fpga-theremin/theremin/teensy4theremin/ltspice/diff_osc_dewster_2020-11-15_experiments_v7.asc

Cant: cap; 8pF
Chand: cap; 0.0001pF
L1: ind; 4mH; Rser=120 Cpar=1.2pF
Q1: npn; 2N3904
Q2: npn; 2N3904
Q3: npn; 2N3904
Q4: npn; 2N3904
Q5: npn; 2N3904
Q6: npn; 2N3904
Q7: npn; 2N3904
Q8: npn; 2N3904
Q9: npn; 2N3904
Q10: npn; 2N3904
Q11: pnp; 2N3906
Q12: pnp; 2N3906
Q13: npn; 2N3904
Q14: pnp; 2N3906
Q15: pnp; 2N3906
Q16: pnp; 2N3906
R1: res; 220
R2: res; 220
R3: res; 2200
R4: res; 1K
R5: res; 330
R6: res; 10
R7: res; 220
R8: res; 10
R10: res; 1
R11: res; 10
Rrf: res; 1Meg
V1: voltage; 3.3v
Named nets: 0, VCC, ANT
.tran 0 1.01m 1m 0.00001m
.IC V(ANT)=1
.MEAS TRAN t1 V(OUT) WHEN V(OUT) = 0 rise=1
.MEAS TRAN t2 V(OUT) WHEN V(OUT) = 0 rise=2
.MEAS TRAN freq21 PARAM 1/(t2-t1)
