fpga-theremin/theremin/teensy4theremin/ltspice/2020_npn_pnp_osc_test_v16.asc

C1: cap; 330pF
C2: cap; 100pF
C3: cap; 330pF
C4: cap; 1µF
C5: cap; 330pF
C6: cap; 330pF
C7: cap; 120pF
C8: cap; 4.7pF
C9: cap; 4.7pF
C10: cap; 0.5pF
C11: cap; 0.5pF
C12: cap; 0.5pF
C13: cap; 0.5pF
C14: cap; 2.2pF
C15: cap; 110pF
C16: cap; 330pF
C17: cap; 75pF
C18: cap; 330pF
Cant1: cap; 8pF
Cant: cap; 8pF
Chand1: cap; 1.5pF
Chand: cap; 1.5pF
D3: diode
D4: diode
D6: diode
D7: diode
L1: ind; 1.8mH; Ipk=0.1 Rser=82 Rpar=20Meg Cpar=1.286pF
L2: ind; 2.2mH; Ipk=0.1 Rser=82 Rpar=20Meg Cpar=1.286pF
Q1: npn; BC847B
Q2: pnp; BC857B
Q3: npn; BC847B
Q4: pnp; BC857B
Q5: npn; BC847B
Q6: npn; BC847B
Q7: pnp; BC857B
Q8: pnp; BC857B
R1: res; 120K
R2: res; 12400K
R3: res; 47
R4: res; 10
R5: res; 47
R6: res; 1200
R7: res; 120K
R8: res; 1200
R9: res; 1
R10: res; 1
R11: res; 47
R12: res; 47
R13: res; 220K
R14: res; 220K
R15: res; 1
R16: res; 2.2K
R17: res; 10
R18: res; 100
R19: res; 2400K
R20: res; 1
R21: res; 220K
R22: res; 1
R23: res; 2.2K
R24: res; 100
R25: res; 1
R26: res; 1.2Meg
V1: voltage; 3.3V
Named nets: 0, ANT, COM, ESD1, ESD2, FLT3V3, OSC_OUT, ANT2
.tran 0 2.5m 0.5m 0.00001m
.IC V(ANT)=1u
.MEAS TRAN t_var1 V(ANT) WHEN V(ANT) = 0 rise=1
.MEAS TRAN t_var2 V(ANT) WHEN V(ANT) = 0 rise=2
.MEAS TRAN f_var PARAM 1/(t_var2-t_var1)
ESD protection
Oscillator
Theremin oscillator - Colpitts with bridge
.ic V(ANT2)=1u
