fpga-theremin/theremin/teensy4theremin/ltspice/2019_analog_oscill_sin_33v_noise_test_v03.asc

C1: cap; 4.7pF
C2: cap; 120pF
C3: cap; 180pF
C4: cap; 10µF
C5: cap; 1pF
C6: cap; 33pF
C7: cap; 1pF
C8: cap; 1.5pF
C9: cap; 1.5pF
C10: cap; 1.5pF
C11: cap; 1.5pF
C12: cap; 1.5pF
C13: cap; 1.5pF
C14: cap; 4.7pF
C15: cap; 2.4nF
C16: cap; 240pF
C17: cap; 1µF
C18: cap; 1µF
Cant1: cap; 4pF
Chand: cap; 0.0001pF
D1: diode
D2: diode
D3: diode
D4: diode
D6: diode
D7: diode
L1: ind; 1.5mH; Ipk=0.1 Rser=120 Rpar=9Meg Cpar=1.76pF
L2: ind; 10µH; Rser=1
L4: ind; 100µH; Rser=10
Q1: npn; 2N3904
Q2: npn; 2N3904
Q3: npn; 2N3904
Q4: pnp; 2N3906
R1: res; 330k
R2: res; 1500
R3: res; 10
R4: res; 470K
R5: res; 180
R6: res; 1Meg
R7: res; 1500
R16: res; 3.6K
R17: res; 220
R18: res; 470
R19: res; 220
R20: res; 100
R21: res; 10
Rant: res; 2.4Meg
V1: voltage; 5V
V10: voltage; SINE(0 0.1 10000 0); Rser=100
V11: voltage; SINE(0 0.1 12725 0); Rser=100
V12: voltage; SINE(0 0.1 16192 0); Rser=100
V13: voltage; SINE(0 0.1 20604 0); Rser=100
V14: voltage; SINE(0 0.1 26218 0); Rser=100
V15: voltage; SINE(0 0.1 33362 0); Rser=100
V16: voltage; SINE(0 0.1 42453 0); Rser=100
V17: voltage; SINE(0 0.1 54020 0); Rser=100
V18: voltage; SINE(0 0.1 68740 0); Rser=100
V19: voltage; SINE(0 0.1 87470 0); Rser=100
V20: voltage; SINE(0 0.1 111303 0); Rser=100
V21: voltage; SINE(0 0.1 141631 0); Rser=100
V22: voltage; SINE(0 0.1 180223 0); Rser=100
V23: voltage; SINE(0 0.1 229330 0); Rser=100
V24: voltage; SINE(0 0.1 291818 0); Rser=100
V25: voltage; SINE(0 0.1 371332 0); Rser=100
V26: voltage; SINE(0 0.1 472512 0); Rser=100
V27: voltage; SINE(0 0.1 601262 0); Rser=100
V28: voltage; SINE(0 0.1 765094 0); Rser=100
V29: voltage; SINE(0 0.1 973566 0); Rser=100
V30: voltage; SINE(0 0.1 1238843 0); Rser=100
V31: voltage; SINE(0 0.1 1576403 0); Rser=100
V32: voltage; SINE(0 0.1 2005940 0); Rser=100
V33: voltage; SINE(0 0.1 2552518 0); Rser=100
V34: voltage; SINE(0 0.1 3248027 0); Rser=100
V35: voltage; SINE(0 0.1 4133048 0); Rser=100
V36: voltage; SINE(0 0.1 5259219 0); Rser=100
V37: voltage; SINE(0 0.1 6692248 0); Rser=100
V38: voltage; SINE(0 0.1 8515749 0); Rser=100
V39: voltage; SINE(0 0.1 10836117 0); Rser=100
V40: voltage; SINE(0 0.1 13788737 0); Rser=100
V41: voltage; SINE(0 0.1 17545886 0); Rser=100
V42: voltage; SINE(0 0.1 22326781 0); Rser=100
V43: voltage; SINE(0 0.1 28410373 0); Rser=100
V44: voltage; SINE(0 0.1 36151619 0); Rser=100
V45: voltage; SINE(0 0.1 46002197 0); Rser=100
V46: voltage; SINE(0 0.1 58536855 0); Rser=100
V47: voltage; SINE(0 0.1 74486952 0); Rser=100
V48: voltage; SINE(0 0.1 94783124 0); Rser=100
V49: voltage; SINE(0 0.1 120609589 0); Rser=100
Named nets: 0, ANT, OSC_OUT, COM, ESD1, OUT, ESD2, OUT_FLT, TEST_SINES
.tran 0 21m 1m
.IC V(ANT)=1u
.MEAS TRAN t_var1 V(ANT) WHEN V(ANT) = 0 rise=1
.MEAS TRAN t_var2 V(ANT) WHEN V(ANT) = 0 rise=2
.MEAS TRAN f_var PARAM 1/(t_var2-t_var1)
ESD protection SP721
