fpga-theremin/theremin/teensy4theremin/ltspice/2020_filter_experiments_v2.asc

C1: cap; 1.6nF
C2: cap; 820pF
C3: cap; 1.6nF
C4: cap; 820pF
C5: cap; 1.6nF
L1: ind; 22µH; Rser=1
L2: ind; 47µH; Rser=2
L3: ind; 22µH; Rser=1
L4: ind; 47µH; Rser=2
L5: ind; 22µH; Rser=1
R1: res; 100
R2: res; 1000
V1: voltage; SINE(0 1 {FTEST}); Rser=1
Named nets: 0, OUT
.tran 0 9m 1m 0.0000001m
.STEP PARAM FTEST LIST 50000 58229 67813 78975 91973 107111 124740 145271 169180 197026 229454 267219 311200 362420 422071 491539 572440 666657 776381 904165 1052980 1226289 1428122 1663174 1936913 2255707 2626971 3059340 3562872 4149280 4832204 5627529 6553756 7632429 8888639 10351607 12055363 14039537 16350284 19041353
