fpga-theremin/theremin/teensy4theremin/ltspice/2020_oscillator_experiments_v12.asc

C1: cap; 150pF
C2: cap; 1µF
C7: cap; 0.5pF
C10: cap; 0.5pF
C11: cap; 0.5pF
C12: cap; 0.5pF
C13: cap; 512pF
C14: cap; 0.5pF
C16: cap; 0.5pF
C17: cap; 0.5pF
C18: cap; 0.5pF
C21: cap; 224pF
C23: cap; 0.1µF
C_ant: cap; 8pF
C_hand: cap; 0.01pF
C_sense: cap; 1pF
D1: diode
D2: diode
D3: diode
D4: diode
D5: diode
D6: diode
D7: diode
D8: diode
L1: ind; 3mH; Rser=120 Rpar=20Meg
L4: ind; 128µH; Rser=10
L5: ind; 61µH; Rser=5
R4: res; 1000
R5: res; 1000
R7: res; 1
R10: res; 3300
R16: res; 100
R19: res; 100
R20: res; 1000
R_loss: res; 2400K
R_sense: res; 3.6
U1: OPA350
U2: ad8611
V1: voltage; 3.3V
Named nets: 0, COM, ESD1, ESD2, ANT, L_IN2, L_OUT, ESD3, ESD4, FLT_OUT
.tran 0 1.3m 1m 0.000001m
.IC V(ANT)=1u
