fpga-theremin/theremin/teensy4theremin/ltspice/2020_npn_pnp_osc_v16_tune_4.asc

C1: cap; 82pF
C2: cap; 10pF
C3: cap; 150pF
C4: cap; 1µF
C5: cap; 82pF
C6: cap; 150pF
C8: cap; 10pF
C9: cap; 10pF
C10: cap; 0.5pF
C11: cap; 0.5pF
C12: cap; 0.5pF
C13: cap; 0.5pF
C14: cap; 150pF
Cant: cap; 8pF
Chand: cap; 100pF
D3: diode
D4: diode
D6: diode
D7: diode
L1: ind; 1.5mH; Ipk=0.1 Rser=40 Rpar=20Meg Cpar=1.286pF
Q1: npn; BC847B
Q2: pnp; BC857B
R1: res; 470K
R2: res; 2700K
R3: res; 47
R4: res; 10
R5: res; 47
R6: res; 15K
R7: res; 470K
R8: res; 15K
V1: voltage; 3.3V
Named nets: 0, ANT, COM, ESD1, ESD2, FLT3V3, OSC_OUT
.tran 0 8.1m 0.6m 0.00001m
.IC V(ANT)=1u
.MEAS TRAN t_var1 V(ANT) WHEN V(ANT) = 0 rise=1
.MEAS TRAN t_var2 V(ANT) WHEN V(ANT) = 0 rise=2
.MEAS TRAN f_var PARAM 1/(t_var2-t_var1)
ESD protection
Oscillator
Theremin oscillator - Colpitts with bridge
