fpga-theremin/theremin/teensy4theremin/ltspice/2020_npn_pnp_osc_v16_tune.asc

C1: cap; 330pF
C3: cap; 330pF
C4: cap; 1µF
C5: cap; 330pF
C6: cap; 330pF
C8: cap; 4.7pF
C9: cap; 4.7pF
C10: cap; 0.5pF
C11: cap; 0.5pF
C12: cap; 0.5pF
C13: cap; 0.5pF
Cant: cap; 8pF
Chand: cap; 0.1pF
D3: diode
D4: diode
D6: diode
D7: diode
L1: ind; 1.8mH; Ipk=0.1 Rser=82 Rpar=20Meg Cpar=1.286pF
Q1: npn; BC847B
Q2: pnp; BC857B
R1: res; 120K
R2: res; 2700K
R3: res; 47
R4: res; 10
R5: res; 47
R6: res; 1000
R7: res; 120K
R8: res; 1000
V1: voltage; 3.3V
Named nets: 0, ANT, COM, ESD1, ESD2, FLT3V3, OSC_OUT
.tran 0 1.1m 0.1m 0.00001m
.IC V(ANT)=1u
.MEAS TRAN t_var1 V(ANT) WHEN V(ANT) = 0 rise=1
.MEAS TRAN t_var2 V(ANT) WHEN V(ANT) = 0 rise=2
.MEAS TRAN f_var PARAM 1/(t_var2-t_var1)
ESD protection
Oscillator
Theremin oscillator - Colpitts with bridge
