fpga-theremin/theremin/teensy4theremin/ltspice/2020_analog_oscill_npn_experiments_33v_v05.asc

C1: cap; 1pF
C2: cap; 2.2pF
C3: cap; 2.2pF
C4: cap; 1µF
C5: cap; 1pF
C6: cap; 220pF
C7: cap; 220pF
C8: cap; 0.5pF
C9: cap; 0.5pF
C10: cap; 0.5pF
C11: cap; 0.5pF
C12: cap; 0.5pF
C13: cap; 0.5pF
C15: cap; 22pF
Cant: cap; 8pF
Chand: cap; {CHAND}
D1: diode
D2: diode
D3: diode
D4: diode
D6: diode
D7: diode
L1: ind; 2.2mH; Ipk=0.1 Rser=69 Rpar=1.536Meg Cpar=1.147pF
Q1: npn; 2N3904
Q2: npn; 2N3904
R1: res; 470
R2: res; 100K
R3: res; 100K
R4: res; 10
R5: res; 470
R7: res; 33K
Rant: res; 4.7Meg
V1: voltage; 3.3V
Named nets: 0, ANT, COM, ESD1, ESD2, ESD3, OUT_SIN2, OUT
.tran 0 4m 3m 0.001m
.STEP PARAM CHAND LIST 0pF 1.5pF
.IC V(ANT)=1u
.MEAS TRAN t_var1 V(ANT) WHEN V(ANT) = 0 rise=1
.MEAS TRAN t_var2 V(ANT) WHEN V(ANT) = 0 rise=2
.MEAS TRAN f_var PARAM 1/(t_var2-t_var1)
ESD protection SP721
