fpga-theremin/theremin/teensy4theremin/ltspice/phase_shift_sensor_2500uH_serial_lc_v5_0125mm_experiments.asc

C1: cap; 3.3pF
C2: cap; 220pF
C3: cap; 3.3pF
C4: cap; 3.3pF
C6: cap; 0.5pF
C7: cap; 0.5pF
C8: cap; 0.5pF
C9: cap; 0.5pF
Cant: cap; 8pF
Chand: cap; {Chand}
D3: diode
D4: diode
D5: diode
D6: diode
L1: ind; 2500µH; Ipk=0.01 Rser=79 Rpar=2.828Meg Cpar=1.166pF
R1: res; 10
R2: res; 220K
R3: res; 220K
R4: res; 4.7Meg
U1: 74AHC1G04
U2: 74AHC1G04
U3: 74AHC1G04
U4: 74AHC1G14
U5: 74AHC1G04
U6: 74AHC1G04
V1: voltage; 3.3V
V2: voltage; PULSE(0 3.3 0 0.00000001 0.00000001 0.000000500 0.000001000)
V3: voltage; 3.3V
Named nets: 0, FREF, ANT, COM, FSHIFT, OUT_SHIFTED, FREF_BUF, 5V
.tran 0 0.000305 0.0003 0.000000001
.step param Chand list 0pF 0.025pF 0.05pF 0.075pF 0.1pF 0.125pF 0.15pF 0.175pF 0.2pF 0.225pF 0.25pF 0.275pF 0.3pF 0.325pF 0.35pF 0.375pF 0.4pF 0.425pF 0.45pF 0.475pF 0.5pF 0.525pF 0.55pF 0.575pF 0.6pF 0.625pF 0.65pF 0.675pF 0.7pF 0.725pF 0.75pF 0.775pF 0.8pF 0.825pF 0.85pF 0.875pF 0.9pF 0.925pF 0.95pF 0.975pF 1pF 1.025pF 1.05pF 1.075pF 1.1pF 1.125pF 1.15pF 1.175pF 1.2pF 1.225pF 1.25pF 1.275pF 1.3pF 1.325pF 1.35pF 1.375pF 1.4pF 1.425pF 1.45pF 1.475pF 1.5pF 1.525pF 1.55pF 1.575pF 1.6pF 1.625pF 1.65pF 1.675pF 1.7pF 1.725pF 1.75pF 1.775pF 1.8pF 1.825pF 1.85pF 1.875pF 1.9pF 1.925pF 1.95pF 1.975pF 2.0pF
Ref clock ~0.5..1.5 MHz 3.3V
Phase Shift Theremin Sensor
Air core 32mm plastic frame 0.125 mm copper wire 
coil-to-coil, 53mm winding length
ESD protection SP721
Calibration: with hand FAR from antenna,
choose FREF so phase shift of output changes maximally 
when C_hand changes by smal value
Simulate for hand C from 0 to 2pF with 0.025pF step
