fpga-theremin/theremin/hardware/oscillator/2018_09_colpitts_npn_oscillator_v3.asc

C1: cap; 4.7pF
C2: cap; 220pF
C3: cap; 220pF
C4: cap; 1µF
C5: cap; 0.1µF
C6: cap; 3.5pF
C7: cap; 3.5pF
C8: cap; 0.01µF
C10: cap; 1pF
C12: cap; 3.5pF
C13: cap; 3.5pF
Cant: cap; 7pF
D1: diode
D2: diode
D7: diode
D8: diode
L1: ind; 1.45mH; Ipk=0.1 Rser=65 Rpar=20Meg Cpar=0.85pF
R1: res; 470k
R2: res; 2.7k
R3: res; 100
R4: res; 1Meg
R5: res; 1Meg
Rant: res; 10meg
U1: npn; BC547C
U2.1: 74hc04; VCC=3.3  SPEED=1.0  TRIPDT=1e-9
U2.2: 74hc04; VCC=3.3  SPEED=1.0  TRIPDT=1e-9
V1: voltage; 3.3v
Named nets: 0, 3.3V, ANT, OUT_OSC, OUT, ESD1, ESD2
.tran 0 15m 1m
.IC V(ANT)=1u
.MEAS TRAN t_var1 V(ANT) WHEN V(ANT) = 0 rise=1
.MEAS TRAN t_var2 V(ANT) WHEN V(ANT) = 0 rise=2
.MEAS TRAN f_var PARAM 1/(t_var2-t_var1)
Digital Theremin Sensor Oscillator v0.1
ESD protection diode array, e.g. DALC208SC6
Oscillator
Output buffer
