fpga-theremin/theremin/teensy4theremin/ltspice/2020_current_sense_lt1713.asc

C2: cap; 10µF
C_ant: cap; 10pF
L1: ind; 4.624mH; Rser=120 Rpar=10Meg Cpar=1.216pF
R1: res; 1
R2: res; 10000
R3: res; 1
R4: res; 1
R5: res; 1
R_loss: res; 7000K
R_sense: res; 47
U1: LT1713
U2: max961b
V1: voltage; 3.3V
Named nets: 0, COM, ANT
.tran 0 1m 0.01m
.IC V(ANT)=1u
