fpga-theremin/theremin/teensy4theremin/ltspice/2020_current_sense_lt1809_v01.asc

C2: cap; 10µF
C_ant: cap; 8pF
L1: ind; 4.624mH; Rser=120 Rpar=100Meg Cpar=1.216pF
R1: res; 1
R2: res; 330
R3: res; 100
R4: res; 100
R_loss: res; 7000K
R_sense: res; 22
U1: LT6200-10
V1: voltage; 4.5V
Named nets: 0, COM, ANT
.tran 0 3m 1m 0.00001m
.IC V(ANT)=1u
