fpga-theremin/theremin/teensy4theremin/ltspice/2020_current_sense_lt6200_v02.asc

C2: cap; 10µF
C_ant: cap; 10pF
L1: ind; 4.624mH; Rser=120 Rpar=100Meg Cpar=1.216pF
R1: res; 1
R2: res; 2k
R3: res; 470
R4: res; 470
R5: res; 1
R_loss: res; 7000K
R_sense: res; 100
U1: opa354
V1: voltage; 4.5V
Named nets: 0, COM, ANT
.tran 0 3m 1m 0.00001m
.IC V(ANT)=1u
