fpga-theremin/theremin/teensy4theremin/ltspice/2020_current_sense_npn_pnp_v03.asc

C1: cap; 10000pF
C2: cap; 1pF
C3: cap; 1pF
C_ant: cap; 10pF
D1: diode
D2: diode
L1: ind; 4.624mH; Rser=120 Rpar=100Meg Cpar=1.216pF
Q1: pnp; BC557C
Q2: npn; BC547C
Q3: npn; BC547C
Q8: pnp; BC557C
Q10: pnp; BC557C
Q11: pnp; BC557C
Q12: pnp; BC557C
Q13: pnp; BC557C
Q14: npn; BC547C
Q15: npn; BC547C
Q16: npn; BC547C
Q17: npn; BC547C
Q18: npn; BC547C
R1: res; 100
R3: res; 22
R4: res; 22
R6: res; 100K
R7: res; 1K
R8: res; 1K
R9: res; 100K
R10: res; 10
R11: res; 1K
R12: res; 10
R13: res; 4.7K
R_loss: res; 7500K
R_sense: res; 33
U1: 74AHC1G04
V1: voltage; 4.5V
V2: voltage; 3.3V
Named nets: 0, COM, ANT, OUT
.tran 0 0.503m 0.5m 0.00001m
.IC V(ANT)=1u
