fpga-theremin/theremin/teensy4theremin/ltspice/2020_pll_4046_v01.asc

C1: cap; 10nF
C2: cap; 3300pF
C3: cap; 0.1µF
C_ant1: cap; 10pF
L1: ind; 4.624mH; Rser=120 Rpar=10Meg Cpar=1.216pF
R1: res; 22K
R3: res; 27K
R4: res; 1K
R6: res; 4.3K
R7: res; 100K
R13: res; 1K
R_loss1: res; 7000K
R_sense: res; 33
U1: opa354
U2: 74HC4046TI
U3: opa354
U4: opa354
V1: voltage; 5V
Named nets: COM, 0, ANT, VCOCTL
.tran 0 3m 0.001m
