fpga-theremin/theremin/teensy4theremin/ltspice/2020_current_sense_comparator_npn_v09.asc

C2: cap; 22µF
C_ant: cap; 9.8pF
L1: ind; 2.624mH; Rser=66 Cpar=1.216pF
Q1: npn; BC547C
Q2: npn; BC547C
Q3: npn; BC547C
Q4: npn; BC547C
Q5: npn; BC547C
Q6: npn; BC547C
Q7: npn; BC547C
Q8: npn; BC547C
Q9: npn; BC547C
R1: res; 1
R3: res; 270
R4: res; 100
R16: res; 4.,7K
R19: res; 4.7K
R_loss: res; 7.6Meg
R_sense: res; 47
V1: voltage; 4.5V
Named nets: 0, COM, ANT, Drive, diff1, OUT
.tran 0 3m 1m 0.00001m
.IC V(ANT)=1u
