fpga-theremin/theremin/teensy4theremin/ltspice/2020_current_sense_ad6362_v02.asc

C1: cap; 150pF
C2: cap; 0.1µF
C3: cap; 0.1µF
C4: cap; 10pF
C5: cap; 0.1µF
C_ant: cap; 8pF
L1: ind; 2.624mH; Rser=60 Rpar=10Meg Cpar=1.216pF
Q1: pnp; BC557C
Q2: npn; BC547C
R1: res; 1
R2: res; 10K
R3: res; 10K
R4: res; 4.7K
R5: res; 4.7K
R6: res; 1
R7: res; 22K
R8: res; 22K
R9: res; 100
R10: res; 100
R11: res; 100
R_loss: res; 1000K
R_sense: res; 100
U1: LTC6362
U2: LTC6362
V1: voltage; 4.5V
Named nets: 0, COM, ANT
.tran 0 3m 1m 0.00001m
.IC V(ANT)=1u
