fpga-theremin/theremin/teensy4theremin/ltspice/2020_current_sense_comparator_ltc6362_v04.asc

C1: cap; 3pF
C2: cap; 0.1µF
C3: cap; 3pF
C4: cap; 220pF
C5: cap; 1nF
C6: cap; 100pF
C7: cap; 100pF
C8: cap; 100pF
C9: cap; 1nF
C10: cap; 10pF
C11: cap; 10pF
C12: cap; 1000pF
C_ant: cap; 8pF
L1: ind; 2.624mH; Rser=66 Rpar=10Meg Cpar=1.216pF
R1: res; 1
R2: res; 10K
R3: res; 10K
R4: res; 1000
R6: res; 22K
R7: res; 22K
R8: res; 100
R9: res; 100
R10: res; 100
R11: res; 470K
R12: res; 1000
R13: res; 1000
R14: res; 33k
R15: res; 33k
R17: res; 1
R_loss: res; 1Meg
R_sense: res; 100
U1: LTC6362
U2: LTC6362
V1: voltage; 3.3V
Named nets: 0, COM, ANT
.tran 0 1.5m 0.5m 0.00001m
.IC V(ANT)=1u
