fpga-theremin/theremin/teensy4theremin/ltspice/2020_current_sense_comparator_npn_pnp_v03.asc

C1: cap; 10nF
C2: cap; 0.1µF
C3: cap; 10nF
C4: cap; 10nF
C5: cap; 1nF
C6: cap; 100pF
C7: cap; 100pF
C8: cap; 100pF
C_ant: cap; 8pF
L1: ind; 2.624mH; Rser=66 Rpar=10Meg Cpar=1.216pF
Q1: npn; BC847C
Q2: npn; BC847C
Q3: npn; BC847C
Q4: npn; BC847C
Q5: pnp; BC857C
Q6: pnp; BC857C
Q7: pnp; BC857C
Q8: pnp; BC857C
Q9: npn; BC847C
Q10: pnp; BC857C
R1: res; 1
R2: res; 10K
R3: res; 10K
R4: res; 100
R5: res; 100
R6: res; 68K
R7: res; 68K
R8: res; 100
R9: res; 100
R10: res; 100
R11: res; 470K
R16: res; 4.7K
R18: res; 4.7K
R19: res; 4.7K
R_loss: res; 1Meg
R_sense: res; 100
U2: LTC6362
V1: voltage; 3.3V
Named nets: 0, COM, ANT, OUT, diff1, diff2
.tran 0 1.5m 1m 0.000001m
.IC V(ANT)=1u
