fpga-theremin/theremin/teensy4theremin/ltspice/2020_current_sense_comparator_sine_drive_osc_v01.asc

C1: cap; 1µF
C2: cap; 1µF
C7: cap; 0.5pF
C10: cap; 0.5pF
C_ant: cap; 8pF
C_hand: cap; 0.0001pF
D1: diode
D2: diode
L1: ind; 2.4mH; Rser=85 Rpar=10Meg Cpar=1.216pF
Q1: npn; 2N3904
Q2: pnp; 2N3906
Q3: npn; 2N3904
Q4: pnp; 2N3906
R1: res; 1
R2: res; 10K
R3: res; 10K
R4: res; 2.2K
R5: res; 1
R6: res; 2.2K
R7: res; 2.2K
R8: res; 2.2K
R9: res; 100
R10: res; 100
R11: res; 100
R47: res; 22
R_loss: res; 12400K
U2: ad8137
U7: LT1711
V1: voltage; 3.3V
V2: voltage; 3.3V
Named nets: 0, COM, ESD1, ANT, OUTN, OUTP
.tran 0 3.5m 1.5m 0.0001m
.IC V(ANT)=1u
