fpga-theremin/theremin/teensy4theremin/ltspice/2020_current_sense_comparator_square_drive_osc_v06_lt1711.asc

C1: cap; 10µF
C7: cap; 0.5pF
C10: cap; 0.5pF
C_ant: cap; 8pF
C_hand: cap; 0.0001pF
D1: diode
D2: diode
L1: ind; 2.4mH; Rser=85 Rpar=10Meg Cpar=1.216pF
R1: res; 1
R2: res; 100
R3: res; 100
R4: res; 100
R5: res; 100
R6: res; 100
R7: res; 100
R8: res; 1000
R9: res; 10
R47: res; 100
R_loss: res; 1000K
U7: LT1711
V1: voltage; 3.3V
Named nets: 0, COM, ESD1, ANT, POUT, NOUT
.tran 0 1.3m 0.3m 0.00001m
.IC V(ANT)=1u
