fpga-theremin/theremin/teensy4theremin/ltspice/2020_current_sense_comparator_square_drive_osc_v07.asc

C1: cap; 10µF
C2: cap; 820pF
C3: cap; 3.3nF
C4: cap; 820pF
C5: cap; 0.1µF
C6: cap; 0.1µF
C7: cap; 1pF
C10: cap; 1pF
C_ant: cap; 10pF
C_hand: cap; 0.0001pF
D1: diode
D2: diode
L1: ind; 2.4mH; Rser=85 Rpar=10Meg Cpar=1.216pF
L2: ind; 33µH; Rser=5
L3: ind; 8.2µH; Rser=3
L4: ind; 33µH; Rser=5
R1: res; 1
R2: res; 100
R3: res; 100
R4: res; 100
R5: res; 100
R6: res; 1000
R47: res; 22
R_loss: res; 2400K
U1: LTC6752
U2: LTC6754
V1: voltage; 3.3V
Named nets: 0, COM, ESD1, ANT, OUT, OUTP, OUTN
.tran 0 5.2m 0.2m 0.00001m
.IC V(ANT)=1
