fpga-theremin/theremin/teensy4theremin/ltspice/2020_current_sense_comparator_square_drive_osc_v09_simple.asc

C1: cap; 8pF
L1: ind; 2.624mH; Rser=66 Rpar=10Meg Cpar=1.216pF
R2: res; 100
R3: res; 470
R_loss: res; 2Meg
R_sense: res; 47
U7: LT1711
V1: voltage; 3.3V
Named nets: 0, COM, OUT, ANT
.tran 0 1.3m 0.3m 0.000001m
.IC V(ANT)=1u
