fpga-theremin/theremin/teensy4theremin/ltspice/2020_current_sense_comparator_square_drive_sine_out_osc_v02.asc

C1: cap; 1µF
C2: cap; 0.1µF
C3: cap; 100pF
C4: cap; 100pF
C5: cap; 150pF
C7: cap; 0.5pF
C10: cap; 0.5pF
C_ant: cap; 8pF
C_hand: cap; 0.001pF
D1: diode
D2: diode
L1: ind; 2.4mH; Rser=85 Rpar=10Meg Cpar=1.216pF
R1: res; 1
R2: res; 47
R3: res; 47K
R4: res; 47K
R5: res; 15K
R6: res; 15K
R7: res; 47
R8: res; 1000
R9: res; 100
R10: res; 220
R11: res; 470K
R47: res; 100
R_loss: res; 2200K
U1: LT1711
U3: LTC6362
V1: voltage; 3.3V
Named nets: 0, COM, ESD1, ANT, outp, outn
.tran 0 1.2m 0.2m 0.00001m
.IC V(ANT)=1
