fpga-theremin/theremin/teensy4theremin/ltspice/diff_osc_2020-11-15.asc

C1: cap; 0.01µf
Cant: cap; 10pF
L1: ind; 4mH
Q1: npn; 2N3904
Q2: npn; 2N3904
Q3: npn; 2N3904
Q4: npn; 2N3904
Q5: npn; 2N3904
Q6: npn; 2N3904
R1: res; 47
R2: res; 4.7k
R3: res; 4.7k
R4: res; 100
R5: res; 4.7k
R6: res; 100
Rrf: res; 1Meg
V1: voltage; 3.3v
Named nets: 0, VCC, OUT
.TRAN 0 1m 0.997m
.IC V(OUT)=0
.MEAS TRAN t1 V(OUT) WHEN V(OUT) = 0 rise=1
.MEAS TRAN t2 V(OUT) WHEN V(OUT) = 0 rise=2
.MEAS TRAN freq21 PARAM 1/(t2-t1)
