fpga-theremin/theremin/teensy4theremin/ltspice/2020_current_sense_bjt_v04.asc

C1: cap; 8pF
C2: cap; 0.1µF
C3: cap; 220pF
C4: cap; 220pF
L1: ind; 2mH; Rser=85 Rpar=10Meg Cpar=1.216pF
Q1: npn; 2N3904
Q2: npn; 2N3904
Q3: npn; 2N3904
Q4: npn; 2N3904
Q5: pnp; 2N3906
Q6: pnp; 2N3906
Q7: pnp; 2N3906
Q8: npn; 2N3904
R1: res; 100
R2: res; 10K
R3: res; 10K
R6: res; 22
R7: res; 1K
R8: res; 470
R_loss: res; 2.4Meg
U1: LT1711
V1: voltage; 3.3V
Named nets: 0, COM, OUT
.tran 0 2.3m 0.3m 0.000001m
