fpga-theremin/theremin/teensy4theremin/ltspice/2020_current_sense_sin_v01.asc

C1: cap; 8pF
C2: cap; 820pF
C3: cap; 2.4nF
C4: cap; 8pF
L1: ind; 2mH; Rser=85 Rpar=10Meg Cpar=1.216pF
L2: ind; 24µH
L3: ind; 8.2µH
L4: ind; 2mH; Rser=85 Rpar=10Meg Cpar=1.216pF
R1: res; 100
R2: res; 100
R6: res; 12
R_loss1: res; 2.4Meg
R_loss: res; 2.4Meg
U1: LT1711
V1: voltage; 3.3V
Named nets: 0, COM, OUTP, OUTN
.tran 0 2.3m 0.3m 0.000001m
