fpga-theremin/theremin/teensy4theremin/ltspice/2020_current_sense_comparator_sin_drive_analod_diff_out_osc_v01.asc

C1: cap; 10µF
C2: cap; 390pF
C3: cap; 5.6nF
C5: cap; 0.1µF
C6: cap; 390pF
C7: cap; 0.5pF
C10: cap; 0.5pF
C_ant: cap; 8pF
C_hand: cap; 0.0001pF
D1: diode
D2: diode
L1: ind; 2.4mH; Rser=85 Rpar=10Meg Cpar=1.216pF
L2: ind; 56µH; Rser=8
L3: ind; 3.9µH; Rser=2.5
L5: ind; 56µH; Rser=8
R1: res; 1
R2: res; 1
R3: res; 1
R7: res; 1.3K
R8: res; 100
R10: res; 100
R11: res; 100
R13: res; 100
R_loss: res; 2400K
R_sense: res; 12
U1: AD1580
U7: LT1711
V1: voltage; 3.3V
Named nets: 0, COM, ESD1, ANT, OUTP, VREF, DRIVE, OUTN, AOUTP, AOUTN
.tran 0 1.3m 0.3m 0.00001m
.IC V(ANT)=1u
Bandpass filter: F_osc/1.3,,F_osc*1.3
Reference voltage 1.25V
Differential Sine output 
-500..+500mV
Current Sensing Theremin Oscillator on LT1711
