fpga-theremin/theremin/teensy4theremin/ltspice/2020_analog_theremin_v02.asc

C1: cap; 10µF
C2: cap; 2.4nF
C3: cap; 16nF
C4: cap; 0.1µF
C5: cap; 3.3nF
C6: cap; 6.8nF
C7: cap; 0.5pF
C8: cap; 47nF
C9: cap; 6.8nF
C10: cap; 0.5pF
C11: cap; 3nF
C12: cap; 2.2nF
C13: cap; 1nF
C_ant: cap; 8pF
C_hand: cap; 0.0001pF
C_tune: cap; 3.5pF
D1: diode
D2: diode
L1: ind; 2.266mH; Rser=80 Rpar=20Meg
L2: ind; 160µH; Rser=3
L3: ind; 24µH; Rser=0.5
L4: ind; 120µH; Rser=3
L5: ind; 240µH; Rser=3
L6: ind; 33µH; Rser=0.5
L7: ind; 240µH; Rser=3
Q1: npn; 2N3904
Q2: pnp; 2N3906
R1: res; 1
R2: res; 100
R3: res; 100
R4: res; 100
R5: res; 200
R6: res; 200
R7: res; 100
R8: res; 200
R9: res; 200
R10: res; 100
R11: res; 2000
R12: res; 2000
R13: res; 470
R14: res; 3.3K
R15: res; 1K
R16: res; 1.3K
R47: res; 12
R_loss: res; 2400K
U1: 74hc393
U2: 74hc393
U3: pot; R=25k; T=.99
U4: pot; R=25k; T=.1
U5: LMC555
U6: pot
U7: LT1711
V1: voltage; 5V
V_CRYSTAL_2MHz: voltage; PULSE(0 5 0 1ns 1ns 0.222u 0.5u)
Named nets: 0, COM, ESD1, ANT, OUT, OSC2, OSC4, OSC8, OSC16, REF2, REF4, REF8, REF16, EVEN, ODD
.tran 0 4.3m 0.3m
.IC V(ANT)=1u
