fpga-theremin/theremin/teensy4theremin/kicad/sensor/analog_switch_heterodyne/analog_switch_heterodyne.kicad_pcb

## KiCad design teensy4theremin/kicad/sensor/analog_switch_heterodyne/analog_switch_heterodyne.kicad_pcb (2020-02-23)

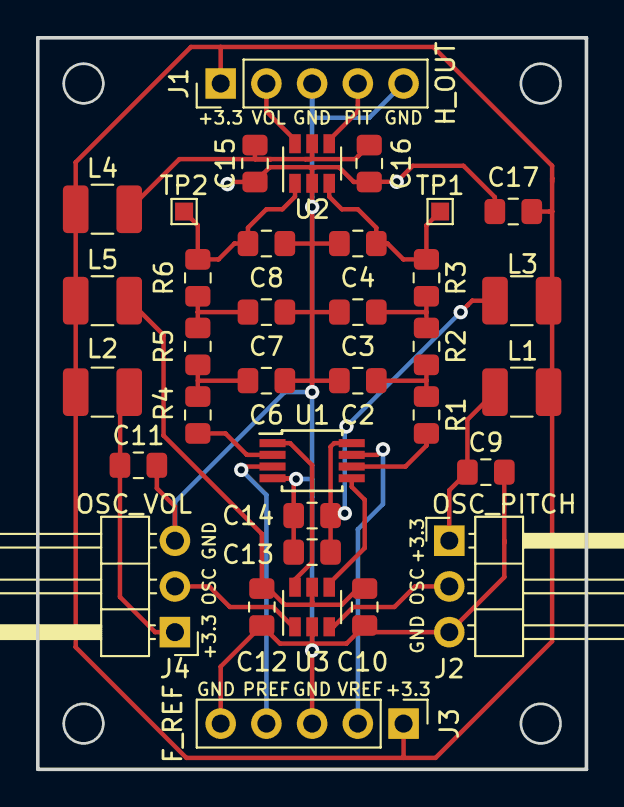
[picture p23: board analog_switch_heterodyne.kicad_pcb from above]

Board: 2 copper layers, 30.5 x 40.6 mm, 35 parts (0 on the bottom side), 23 nets.

Parts:
C2, C3, C4, C6, C7, C8: 100pF; C_0805_2012Metric_Pad1.15x1.40mm_HandSolder
C9, C11, C12, C13, C15: 1uF; C_0805_2012Metric_Pad1.15x1.40mm_HandSolder
C10, C14, C16: 0.1uF; C_0805_2012Metric_Pad1.15x1.40mm_HandSolder
C17: 2.2uF; C_0805_2012Metric_Pad1.15x1.40mm_HandSolder
J1: H_OUT; PinHeader_1x05_P2.54mm_Vertical
J2: OSC_PITCH; PinHeader_1x03_P2.54mm_Horizontal
J3: F_REF; PinHeader_1x05_P2.54mm_Vertical
J4: OSC_VOL; PinHeader_1x03_P2.54mm_Horizontal
L1, L2, L3, L4, L5: Ferrite 10uH; L_1210_3225Metric_Pad1.42x2.65mm_HandSolder
R1, R4: 100; R_0805_2012Metric_Pad1.15x1.40mm_HandSolder
R2, R5: 4.7K; R_0805_2012Metric_Pad1.15x1.40mm_HandSolder
R3, R6: 47K; R_0805_2012Metric_Pad1.15x1.40mm_HandSolder
TP1: PITCH_FLT; TestPoint_Pad_1.0x1.0mm
TP2: VOL_FLT; TestPoint_Pad_1.0x1.0mm
U1: ADG721BRMZ; MSOP-8_3x3mm_P0.65mm
U2, U3: 2G04; SOT-23-6

Connections:
+3V3: C17.1, J1.1, J3.1, L1.1, L2.1, L3.1, L4.1, L5.1
/3.3V_1: C9.1, J2.1, L1.2
/3.3V_2: C11.1, J4.1, L2.2
/FREF_PITCH: J3.4, U1.3
/FREF_VOL: J3.2, U1.7
/HOUT_PITCH: J1.4, U2.4
/HOUT_VOL: J1.2, U2.6
/OSC_PITCH: J2.2, U3.3
/OSC_VOL: J4.2, U3.1
/VCC_U1: C13.1, C14.1, L3.2, U1.8
/VCC_U2: C15.1, C16.1, L4.2, U2.5
/VCC_U3: C10.1, C12.1, L5.2, U3.5
GND: C2.2, C3.2, C4.2, C6.2, C7.2, C8.2, C9.2, C10.2, C11.2, C12.2, C13.2, C14.2, C15.2, C16.2, C17.2, J1.3, J1.5, J2.3, J3.3, J3.5, J4.3, U1.4, U2.2, U3.2
unnamed: C2.1, R1.1, R2.2
unnamed: C3.1, R2.1, R3.2
unnamed: C4.1, R3.1, TP1.1, U2.3
unnamed: C6.1, R4.1, R5.2
unnamed: C7.1, R5.1, R6.2
unnamed: C8.1, R6.1, TP2.1, U2.1
unnamed: R1.2, U1.6
unnamed: R4.2, U1.2
unnamed: U1.1, U3.6
unnamed: U1.5, U3.4
