fpga-theremin/theremin/teensy4theremin/kicad/sensor/square_wave_oscillator_3v3/square_wave_oscillator_3v3.kicad_pcb

## KiCad design teensy4theremin/kicad/sensor/square_wave_oscillator_3v3/square_wave_oscillator_3v3.kicad_pcb (2020-02-18)

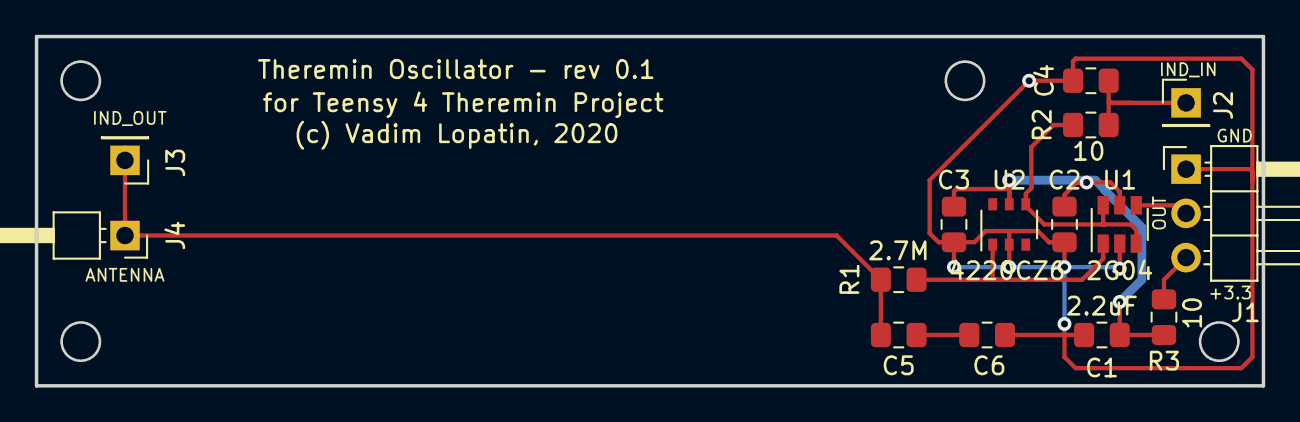
[picture p24: board square_wave_oscillator_3v3.kicad_pcb from above]

Board: 2 copper layers, 70.5 x 20.1 mm, 15 parts (0 on the bottom side), 9 nets.

Parts:
C1: 2.2uF; C_0805_2012Metric_Pad1.15x1.40mm_HandSolder
C2: 0.1uF; C_0805_2012Metric_Pad1.15x1.40mm_HandSolder
C3: 0.22uF; C_0805_2012Metric_Pad1.15x1.40mm_HandSolder
C4, C5, C6: 3.3pF; C_0805_2012Metric_Pad1.15x1.40mm_HandSolder
J1: OSC; PinHeader_1x03_P2.54mm_Horizontal
J2: INDUCTOR_IN; PinHeader_1x01_P2.54mm_Vertical
J3: INDUCTOR_OUT; PinHeader_1x01_P2.54mm_Vertical
J4: ANTENNA; PinHeader_1x01_P2.54mm_Horizontal
R1: 2.7M; R_0805_2012Metric_Pad1.15x1.40mm_HandSolder
R2, R3: 10; R_0805_2012Metric_Pad1.15x1.40mm_HandSolder
U1: 2G04; SOT-23-6
U2: 4220CZ6; TSOP-6_1.65x3.05mm_P0.95mm

Connections:
+3V3: C1.1, C2.1, C3.1, R3.2, U1.5, U2.5
/3.3V: J1.3, R3.1
/OSC_OUT: J1.2, U1.4
GND: C1.2, C2.2, C3.2, C4.1, C6.1, J1.1, U1.2, U2.2
unnamed: C4.2, J2.1, R2.1
unnamed: C5.1, C6.2
unnamed: C5.2, J3.1, J4.1, R1.2
unnamed: R1.1, U1.1, U2.1
unnamed: R2.2, U1.3, U1.6, U2.4
