fpga-theremin/theremin/teensy4theremin/kicad/sensor/phase_shift_sensor_smd_3v3/phase_shift_sensor_smd_3v3.kicad_pcb

## KiCad design teensy4theremin/kicad/sensor/phase_shift_sensor_smd_3v3/phase_shift_sensor_smd_3v3.kicad_pcb (2020-02-14)

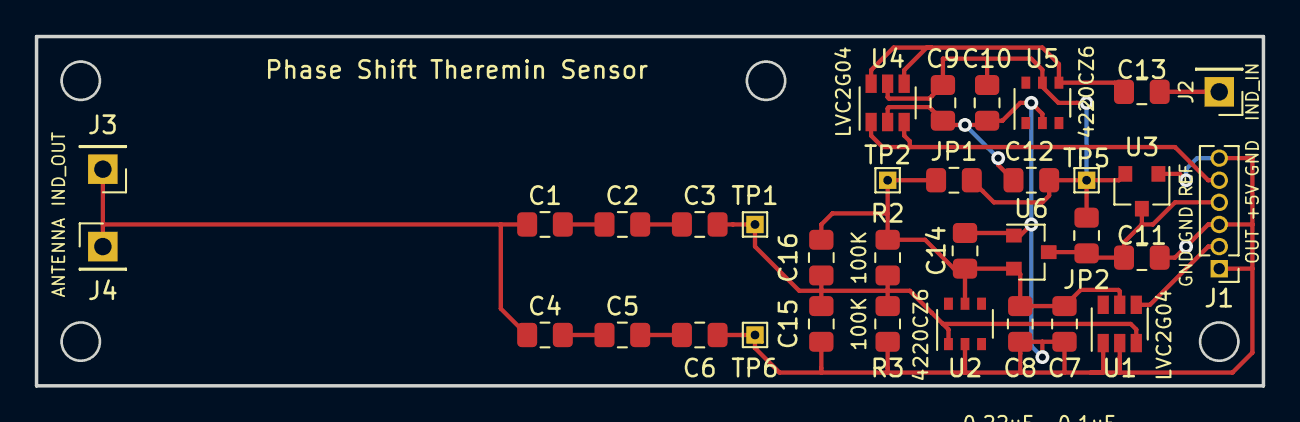
[picture p25: board phase_shift_sensor_smd_3v3.kicad_pcb from above]

Board: 2 copper layers, 70.5 x 20.1 mm, 34 parts (0 on the bottom side), 14 nets.

Parts:
C1, C2, C3, C15, C16: 3.3pF; C_0805_2012Metric_Pad1.15x1.40mm_HandSolder
C4, C5, C6: 10pF; C_0805_2012Metric_Pad1.15x1.40mm_HandSolder
C7, C9: 0.1uF; C_0805_2012Metric_Pad1.15x1.40mm_HandSolder
C8, C10: 0.22uF; C_0805_2012Metric_Pad1.15x1.40mm_HandSolder
C11, C12, C14: 1uF; C_0805_2012Metric_Pad1.15x1.40mm_HandSolder
C13: 220pF; C_0805_2012Metric_Pad1.15x1.40mm_HandSolder
J1: SENSOR; PinHeader_1x06_P1.27mm_Vertical
J2: INDUCTOR_IN; PinHeader_1x01_P2.54mm_Vertical
J3: INDUCTOR_OUT; PinHeader_1x01_P2.54mm_Vertical
J4: ANTENNA; PinHeader_1x01_P2.54mm_Vertical
JP1: 01REG; R_0805_2012Metric_Pad1.15x1.40mm_HandSolder
JP2: 00REG; R_0805_2012Metric_Pad1.15x1.40mm_HandSolder
R2, R3: 100K; R_0805_2012Metric_Pad1.15x1.40mm_HandSolder
TP1: OUT_NOBUF; TestPoint_THTPad_1.0x1.0mm_Drill0.5mm
TP2, TP5: +3.3V; TestPoint_THTPad_1.0x1.0mm_Drill0.5mm
TP6: GND; TestPoint_THTPad_1.0x1.0mm_Drill0.5mm
U1, U4: LVC2G04; SOT-23-6
U2, U5: 4220CZ6; TSOP-6_1.65x3.05mm_P0.95mm
U3, U6: MCP1700-3302E; SOT-23

Connections:
+3V3: C9.1, C10.1, C12.1, JP1.2, JP2.2, TP5.1, U3.2, U4.5, U5.5
+5V: C11.1, J1.4, JP2.1, U3.3, U6.3
/OUT: J1.2, U1.4
/REF_CLK: J1.5, U4.1, U4.3
GND: C6.2, C7.2, C8.2, C9.2, C10.2, C11.2, C12.2, C14.2, C15.2, J1.1, J1.3, J1.6, R3.2, TP6.1, U1.1, U1.2, U2.2, U3.1, U4.2, U5.2, U6.1
unnamed: C1.1, C4.1, J3.1, J4.1
unnamed: C1.2, C2.1
unnamed: C2.2, C3.1
unnamed: C4.2, C5.1
unnamed: C5.2, C6.1
unnamed: C13.1, J2.1
unnamed: C13.2, U4.4, U4.6, U5.4
unnamed: C7.1, C8.1, C14.1, C16.1, JP1.1, R2.1, TP2.1, U1.5, U2.5, U6.2
unnamed: C3.2, C15.1, C16.2, R2.2, R3.1, TP1.1, U1.3, U2.1
