fpga-theremin/theremin/teensy4theremin/kicad/sensor/phase_shift_sensor_proto_simple/phase_shift_sensor_proto_simple.kicad_pcb

## KiCad design teensy4theremin/kicad/sensor/phase_shift_sensor_proto_simple/phase_shift_sensor_proto_simple.kicad_pcb (2019-12-10)

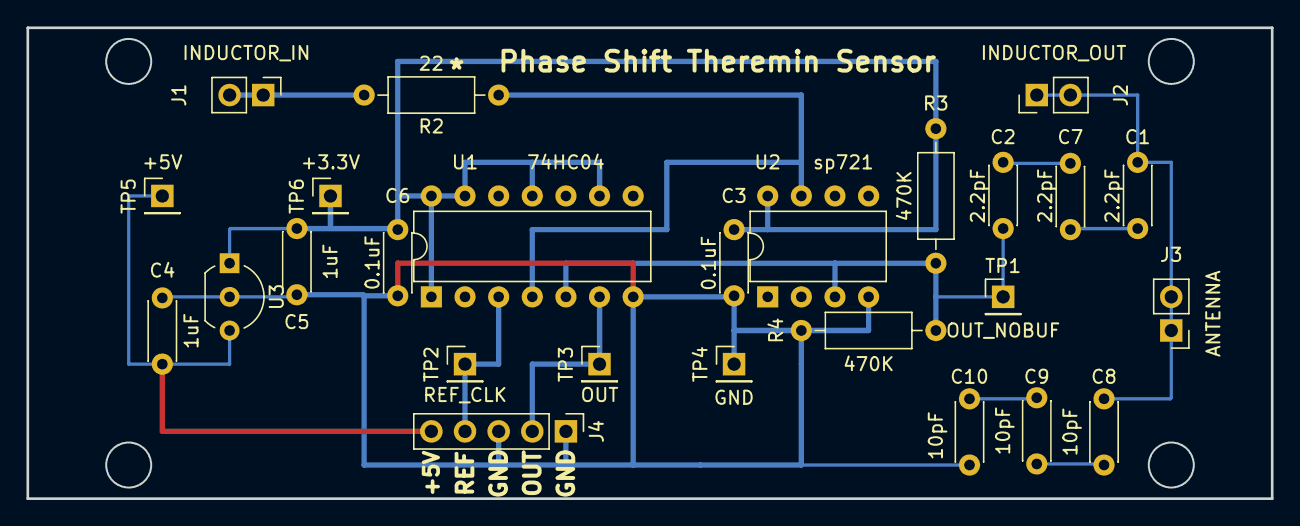
[picture p26: board phase_shift_sensor_proto_simple.kicad_pcb from above]

Board: 2 copper layers, 94.0 x 35.6 mm, 26 parts (0 on the bottom side), 13 nets.

Parts:
C1, C2, C7: 2.2pF; C_Disc_D4.3mm_W1.9mm_P5.00mm
C3, C6: 0.1uF; C_Disc_D4.3mm_W1.9mm_P5.00mm
C4, C5: 1uF; C_Disc_D4.3mm_W1.9mm_P5.00mm
C8, C9, C10: 10pF; C_Disc_D4.3mm_W1.9mm_P5.00mm
J1: INDUCTOR_IN; PinHeader_1x02_P2.54mm_Vertical
J2: INDUCTOR_OUT; PinHeader_1x02_P2.54mm_Vertical
J3: ANTENNA; PinHeader_1x02_P2.54mm_Vertical
J4: SENSOR; PinHeader_1x05_P2.54mm_Vertical
R2: 22; R_Axial_DIN0207_L6.3mm_D2.5mm_P10.16mm_Horizontal
R3, R4: 470K; R_Axial_DIN0207_L6.3mm_D2.5mm_P10.16mm_Horizontal
TP1: OUT_NOBUF; PinHeader_1x01_P2.54mm_Vertical
TP2: REF_CLK; PinHeader_1x01_P2.54mm_Vertical
TP3: OUT; PinHeader_1x01_P2.54mm_Vertical
TP4: GND; PinHeader_1x01_P2.54mm_Vertical
TP5: +5V; PinHeader_1x01_P2.54mm_Vertical
TP6: +3.3V; PinHeader_1x01_P2.54mm_Vertical
U1: 74HC04; DIP-14_W7.62mm
U2: sp721; DIP-8_W7.62mm
U3: L78L33_TO92; TO-92_Inline_Wide

Connections:
+3V3: C3.1, C5.1, C6.1, R3.1, TP6.1, U1.1, U1.9, U1.11, U1.13, U1.14, U2.8, U3.1
+5V: C4.1, J4.5, TP5.1, U3.3
/OUT: J4.2, TP3.1, U1.6
/REF_CLK: J4.4, TP2.1, U1.3
GND: C3.2, C4.2, C5.2, C6.2, C10.1, J4.1, J4.3, R4.2, TP4.1, U1.7, U2.4, U3.2
unnamed: C1.1, C8.2, J2.1, J2.2, J3.1, J3.2
unnamed: C1.2, C7.1
unnamed: C2.1, C7.2
unnamed: C2.2, R3.2, R4.1, TP1.1, U1.5, U2.3
unnamed: C8.1, C9.2
unnamed: C9.1, C10.2
unnamed: J1.1, J1.2, R2.2
unnamed: R2.1, U1.4, U2.7
