fpga-theremin/theremin/teensy4theremin/kicad/sensor/phase_shift_sensor_proto/phase_shift_sensor_proto.kicad_pcb

## KiCad design teensy4theremin/kicad/sensor/phase_shift_sensor_proto/phase_shift_sensor_proto.kicad_pcb (2019-11-25)

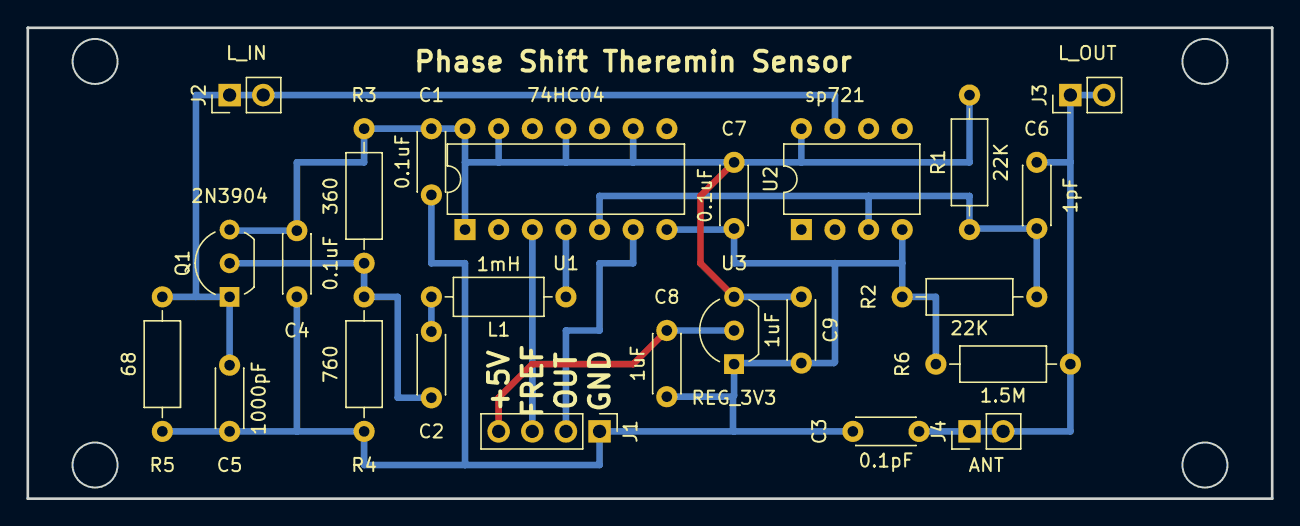
[picture p27: board phase_shift_sensor_proto.kicad_pcb from above]

Board: 2 copper layers, 94.0 x 35.6 mm, 24 parts (0 on the bottom side), 11 nets.

Parts:
C1, C4, C7: 0.1uF; C_Disc_D4.3mm_W1.9mm_P5.00mm
C2: 47pF; C_Disc_D4.3mm_W1.9mm_P5.00mm
C3: 0.1pF; C_Disc_D4.3mm_W1.9mm_P5.00mm
C5: 1000pF; C_Disc_D4.3mm_W1.9mm_P5.00mm
C6: 1pF; C_Disc_D4.3mm_W1.9mm_P5.00mm
C8, C9: 1uF; C_Disc_D4.3mm_W1.9mm_P5.00mm
J1: SENSOR; PinHeader_1x04_P2.54mm_Vertical
J2: L_IN; PinHeader_1x02_P2.54mm_Vertical
J3: L_OUT; PinHeader_1x02_P2.54mm_Vertical
J4: ANT; PinHeader_1x02_P2.54mm_Vertical
L1: 1mH; L_Axial_L6.6mm_D2.7mm_P10.16mm_Horizontal_Vishay_IM-2
Q1: 2N3904; TO-92_Inline_Wide
R1, R2: 22K; R_Axial_DIN0207_L6.3mm_D2.5mm_P10.16mm_Horizontal
R3: 360; R_Axial_DIN0207_L6.3mm_D2.5mm_P10.16mm_Horizontal
R4: 760; R_Axial_DIN0207_L6.3mm_D2.5mm_P10.16mm_Horizontal
R5: 68; R_Axial_DIN0207_L6.3mm_D2.5mm_P10.16mm_Horizontal
R6: 1.5M; R_Axial_DIN0207_L6.3mm_D2.5mm_P10.16mm_Horizontal
U1: 74HC04; DIP-14_W7.62mm
U2: sp721; DIP-8_W7.62mm
U3: REG_3V3; TO-92_Inline_Wide

Connections:
+3V3: C1.1, C4.2, C7.1, C9.1, Q1.3, R1.2, R3.2, U1.1, U1.9, U1.11, U1.13, U1.14, U2.8, U3.3
+5V: C8.1, J1.4, U3.2
/PWM_OUT: J1.2, U1.6
/REF_CLK: J1.3, U1.3
GND: C1.2, C3.1, C4.1, C5.1, C7.2, C8.2, C9.2, J1.1, R2.1, R4.1, R5.1, R6.1, U1.7, U2.4, U3.1
unnamed: C2.1, Q1.2, R3.1, R4.2
unnamed: C2.2, L1.2
unnamed: C3.2, C6.1, J3.1, J3.2, J4.1, J4.2, R6.2
unnamed: C5.2, J2.1, J2.2, Q1.1, R5.2, U2.7
unnamed: C6.2, R1.1, R2.2, U1.5, U2.3
unnamed: L1.1, U1.4
