fpga-theremin/theremin/teensy4theremin/kicad/sensor/opamp_sine_oscillator/opamp_sine_oscillator.kicad_pcb

## KiCad design teensy4theremin/kicad/sensor/opamp_sine_oscillator/opamp_sine_oscillator.kicad_pcb (2019-11-12)

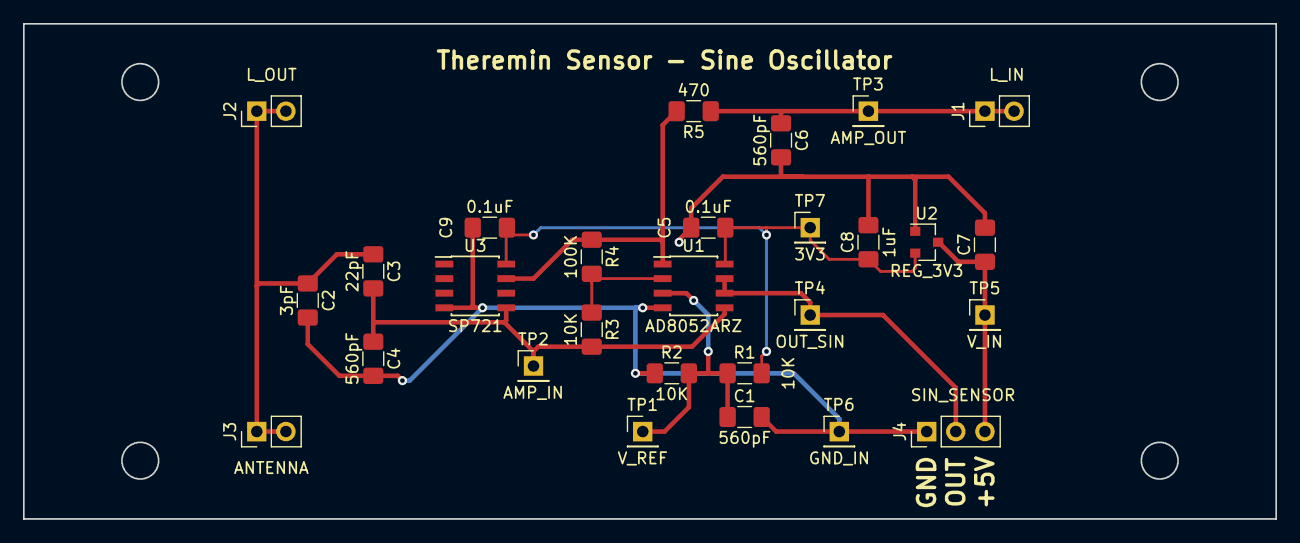
[picture p28: board opamp_sine_oscillator.kicad_pcb from above]

Board: 2 copper layers, 109.2 x 43.2 mm, 28 parts (0 on the bottom side), 10 nets.

Parts:
C1, C4, C6: 560pF; C_1206_3216Metric_Pad1.42x1.75mm_HandSolder
C2: 3pF; C_1206_3216Metric_Pad1.42x1.75mm_HandSolder
C3: 22pF; C_1206_3216Metric_Pad1.42x1.75mm_HandSolder
C5, C9: 0.1uF; C_1206_3216Metric_Pad1.42x1.75mm_HandSolder
C7, C8: 1uF; C_1206_3216Metric_Pad1.42x1.75mm_HandSolder
J1: L_IN; PinHeader_1x02_P2.54mm_Vertical
J2: L_OUT; PinHeader_1x02_P2.54mm_Vertical
J3: ANTENNA; PinHeader_1x02_P2.54mm_Vertical
J4: SIN_SENSOR; PinHeader_1x03_P2.54mm_Vertical
R1, R2, R3: 10K; R_1206_3216Metric_Pad1.42x1.75mm_HandSolder
R4: 100K; R_1206_3216Metric_Pad1.42x1.75mm_HandSolder
R5: 470; R_1206_3216Metric_Pad1.42x1.75mm_HandSolder
TP1: V_REF; PinHeader_1x01_P2.54mm_Vertical
TP2: AMP_IN; PinHeader_1x01_P2.54mm_Vertical
TP3: AMP_OUT; PinHeader_1x01_P2.54mm_Vertical
TP4: OUT_SIN; PinHeader_1x01_P2.54mm_Vertical
TP5: V_IN; PinHeader_1x01_P2.54mm_Vertical
TP6: GND_IN; PinHeader_1x01_P2.54mm_Vertical
TP7: 3V3; PinHeader_1x01_P2.54mm_Vertical
U1: AD8052ARZ; SOIC-8_3.9x4.9mm_P1.27mm
U2: REG_3V3; SOT-23
U3: SP721; SOIC-8_3.9x4.9mm_P1.27mm

Connections:
+3V3: C5.1, C8.1, C9.1, R1.2, TP7.1, U1.8, U2.2, U3.8
+5V: C7.1, J4.3, TP5.1, U2.3
/ESD1: C3.2, C4.1, R3.2, TP2.1, U1.5, U3.5
/ESD2: R4.1, R5.2, U1.1, U3.7
/VREF: C1.1, R1.1, R2.2, TP1.1, U1.3
GND: C1.2, C2.2, C4.2, C5.2, C6.2, C7.2, C8.2, C9.2, J4.1, R2.1, TP6.1, U1.4, U2.1, U3.4
unnamed: C2.1, C3.1, J2.1, J2.2, J3.1, J3.2
unnamed: C6.1, J1.1, J1.2, R5.1, TP3.1
unnamed: J4.2, TP4.1, U1.6, U1.7
unnamed: R3.1, R4.2, U1.2
