fpga-theremin/theremin/teensy4theremin/kicad/sensor/phase_shift_sensor/phase_shift_sensor.kicad_pcb

## KiCad design teensy4theremin/kicad/sensor/phase_shift_sensor/phase_shift_sensor.kicad_pcb (2019-10-14)

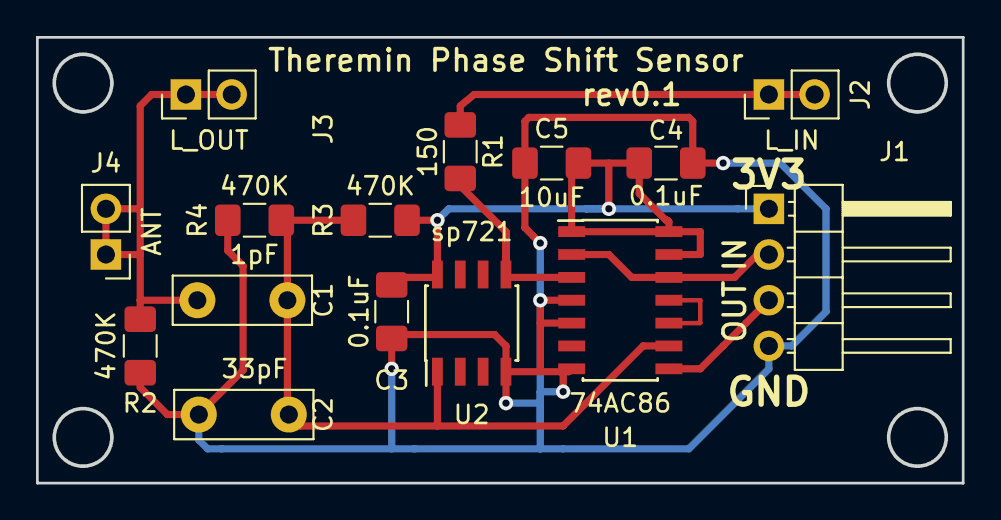
[picture p29: board phase_shift_sensor.kicad_pcb from above]

Board: 2 copper layers, 51.4 x 24.8 mm, 15 parts (0 on the bottom side), 9 nets.

Parts:
C1: 1pF; C_Disc_D7.5mm_W2.5mm_P5.00mm
C2: 33pF; C_Disc_D7.5mm_W2.5mm_P5.00mm
C3, C4: 0.1uF; C_1206_3216Metric_Pad1.42x1.75mm_HandSolder
C5: 10uF; C_1206_3216Metric_Pad1.42x1.75mm_HandSolder
J1: SENSOR; PinHeader_1x04_P2.54mm_Horizontal
J2: L_IN; PinHeader_1x02_P2.54mm_Vertical
J3: L_OUT; PinHeader_1x02_P2.54mm_Vertical
J4: ANT; PinHeader_1x02_P2.54mm_Vertical
R1: 150; R_1206_3216Metric_Pad1.42x1.75mm_HandSolder
R2, R3, R4: 470K; R_1206_3216Metric_Pad1.42x1.75mm_HandSolder
U1: 74AC86; SOIC-14_3.9x8.7mm_P1.27mm
U2: sp721; SOIC-8_3.9x4.9mm_P1.27mm

Connections:
+3V3: C3.1, C4.1, C5.1, J1.1, R3.2, U1.1, U1.13, U1.14, U2.8
/PWM_OUT: J1.3, U1.8
/REF_CLK: J1.2, U1.2, U1.12
GND: C2.2, C3.2, C4.2, C5.2, J1.4, R2.1, R4.1, U1.4, U1.5, U1.7, U2.4
unnamed: C1.1, J3.1, J3.2, J4.1, J4.2, R2.2
unnamed: C1.2, C2.1, R3.1, R4.2, U1.9, U2.1
unnamed: J2.1, J2.2, R1.1
unnamed: R1.2, U1.3, U2.5
unnamed: U1.10, U1.11
