fpga-theremin/theremin/fpga/theremin_hw/theremin_hw.srcs/sources_1/bd/theremin_hw_bd/ip/theremin_hw_bd_auto_pc_0/synth/theremin_hw_bd_auto_pc_0.v

// (c) Copyright 1995-2019 Xilinx, Inc. All rights reserved.
// 
// This file contains confidential and proprietary information
// of Xilinx, Inc. and is protected under U.S. and
// international copyright and other intellectual property
// laws.
// 
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
// CRITICAL APPLICATIONS
// Xilinx products are not designed or intended to be fail-
// safe, or for use in any application requiring fail-safe
// performance, such as life-support or safety devices or
// systems, Class III medical devices, nuclear facilities,
// applications related to the deployment of airbags, or any
// other applications that could lead to death, personal
// injury, or severe property or environmental damage
// (individually and collectively, "Critical
// Applications"). Customer assumes the sole risk and
// liability of any use of Xilinx products in Critical
// Applications, subject only to applicable laws and
// regulations governing limitations on product liability.
// 
// THIS COPYRIGHT NOTICE AND DISCLAIMER MUST BE RETAINED AS
// PART OF THIS FILE AT ALL TIMES.
// 
// DO NOT MODIFY THIS FILE.


// IP VLNV: xilinx.com:ip:axi_protocol_converter:2.1
// IP Revision: 19

(* X_CORE_INFO = "axi_protocol_converter_v2_1_19_axi_protocol_converter,Vivado 2019.1.1" *)
(* CHECK_LICENSE_TYPE = "theremin_hw_bd_auto_pc_0,axi_protocol_converter_v2_1_19_axi_protocol_converter,{}" *)
(* CORE_GENERATION_INFO = "theremin_hw_bd_auto_pc_0,axi_protocol_converter_v2_1_19_axi_protocol_converter,{x_ipProduct=Vivado 2019.1.1,x_ipVendor=xilinx.com,x_ipLibrary=ip,x_ipName=axi_protocol_converter,x_ipVersion=2.1,x_ipCoreRevision=19,x_ipLanguage=VERILOG,x_ipSimLanguage=MIXED,C_FAMILY=zynq,C_M_AXI_PROTOCOL=2,C_S_AXI_PROTOCOL=1,C_IGNORE_ID=0,C_AXI_ID_WIDTH=12,C_AXI_ADDR_WIDTH=32,C_AXI_DATA_WIDTH=32,C_AXI_SUPPORTS_WRITE=1,C_AXI_SUPPORTS_READ=1,C_AXI_SUPPORTS_USER_SIGNALS=0,C_AXI_AWUSER_WIDTH=1,C_AXI_ARUSER_WIDTH=1,C_A\
XI_WUSER_WIDTH=1,C_AXI_RUSER_WIDTH=1,C_AXI_BUSER_WIDTH=1,C_TRANSLATION_MODE=2}" *)
(* DowngradeIPIdentifiedWarnings = "yes" *)
module theremin_hw_bd_auto_pc_0 (
  aclk,
  aresetn,
  s_axi_awid,
  s_axi_awaddr,
  s_axi_awlen,
  s_axi_awsize,
  s_axi_awburst,
  s_axi_awlock,
  s_axi_awcache,
  s_axi_awprot,
  s_axi_awqos,
  s_axi_awvalid,
  s_axi_awready,
  s_axi_wid,
  s_axi_wdata,
  s_axi_wstrb,
  s_axi_wlast,
  s_axi_wvalid,
  s_axi_wready,
  s_axi_bid,
  s_axi_bresp,
  s_axi_bvalid,
  s_axi_bready,
  s_axi_arid,
  s_axi_araddr,
  s_axi_arlen,
  s_axi_arsize,
  s_axi_arburst,
  s_axi_arlock,
  s_axi_arcache,
  s_axi_arprot,
  s_axi_arqos,
  s_axi_arvalid,
  s_axi_arready,
  s_axi_rid,
  s_axi_rdata,
  s_axi_rresp,
  s_axi_rlast,
  s_axi_rvalid,
  s_axi_rready,
  m_axi_awaddr,
  m_axi_awprot,
  m_axi_awvalid,
  m_axi_awready,
  m_axi_wdata,
  m_axi_wstrb,
  m_axi_wvalid,
  m_axi_wready,
  m_axi_bresp,
  m_axi_bvalid,
  m_axi_bready,
  m_axi_araddr,
  m_axi_arprot,
  m_axi_arvalid,
  m_axi_arready,
  m_axi_rdata,
  m_axi_rresp,
  m_axi_rvalid,
  m_axi_rready
);

(* X_INTERFACE_PARAMETER = "XIL_INTERFACENAME CLK, FREQ_HZ 147460937, PHASE 0.0, CLK_DOMAIN /clk_wiz_0_clk_out1, ASSOCIATED_BUSIF S_AXI:M_AXI, ASSOCIATED_RESET ARESETN, INSERT_VIP 0" *)
(* X_INTERFACE_INFO = "xilinx.com:signal:clock:1.0 CLK CLK" *)
input wire aclk;
(* X_INTERFACE_PARAMETER = "XIL_INTERFACENAME RST, POLARITY ACTIVE_LOW, INSERT_VIP 0, TYPE INTERCONNECT" *)
(* X_INTERFACE_INFO = "xilinx.com:signal:reset:1.0 RST RST" *)
input wire aresetn;
(* X_INTERFACE_INFO = "xilinx.com:interface:aximm:1.0 S_AXI AWID" *)
input wire [11 : 0] s_axi_awid;
(* X_INTERFACE_INFO = "xilinx.com:interface:aximm:1.0 S_AXI AWADDR" *)
input wire [31 : 0] s_axi_awaddr;
(* X_INTERFACE_INFO = "xilinx.com:interface:aximm:1.0 S_AXI AWLEN" *)
input wire [3 : 0] s_axi_awlen;
(* X_INTERFACE_INFO = "xilinx.com:interface:aximm:1.0 S_AXI AWSIZE" *)
input wire [2 : 0] s_axi_awsize;
(* X_INTERFACE_INFO = "xilinx.com:interface:aximm:1.0 S_AXI AWBURST" *)
input wire [1 : 0] s_axi_awburst;
(* X_INTERFACE_INFO = "xilinx.com:interface:aximm:1.0 S_AXI AWLOCK" *)
input wire [1 : 0] s_axi_awlock;
(* X_INTERFACE_INFO = "xilinx.com:interface:aximm:1.0 S_AXI AWCACHE" *)
input wire [3 : 0] s_axi_awcache;
(* X_INTERFACE_INFO = "xilinx.com:interface:aximm:1.0 S_AXI AWPROT" *)
input wire [2 : 0] s_axi_awprot;
(* X_INTERFACE_INFO = "xilinx.com:interface:aximm:1.0 S_AXI AWQOS" *)
input wire [3 : 0] s_axi_awqos;
(* X_INTERFACE_INFO = "xilinx.com:interface:aximm:1.0 S_AXI AWVALID" *)
input wire s_axi_awvalid;
(* X_INTERFACE_INFO = "xilinx.com:interface:aximm:1.0 S_AXI AWREADY" *)
output wire s_axi_awready;
(* X_INTERFACE_INFO = "xilinx.com:interface:aximm:1.0 S_AXI WID" *)
input wire [11 : 0] s_axi_wid;
(* X_INTERFACE_INFO = "xilinx.com:interface:aximm:1.0 S_AXI WDATA" *)
input wire [31 : 0] s_axi_wdata;
(* X_INTERFACE_INFO = "xilinx.com:interface:aximm:1.0 S_AXI WSTRB" *)
input wire [3 : 0] s_axi_wstrb;
(* X_INTERFACE_INFO = "xilinx.com:interface:aximm:1.0 S_AXI WLAST" *)
input wire s_axi_wlast;
(* X_INTERFACE_INFO = "xilinx.com:interface:aximm:1.0 S_AXI WVALID" *)
input wire s_axi_wvalid;
(* X_INTERFACE_INFO = "xilinx.com:interface:aximm:1.0 S_AXI WREADY" *)
output wire s_axi_wready;
(* X_INTERFACE_INFO = "xilinx.com:interface:aximm:1.0 S_AXI BID" *)
output wire [11 : 0] s_axi_bid;
(* X_INTERFACE_INFO = "xilinx.com:interface:aximm:1.0 S_AXI BRESP" *)
output wire [1 : 0] s_axi_bresp;
(* X_INTERFACE_INFO = "xilinx.com:interface:aximm:1.0 S_AXI BVALID" *)
output wire s_axi_bvalid;
(* X_INTERFACE_INFO = "xilinx.com:interface:aximm:1.0 S_AXI BREADY" *)
input wire s_axi_bready;
(* X_INTERFACE_INFO = "xilinx.com:interface:aximm:1.0 S_AXI ARID" *)
input wire [11 : 0] s_axi_arid;
(* X_INTERFACE_INFO = "xilinx.com:interface:aximm:1.0 S_AXI ARADDR" *)
input wire [31 : 0] s_axi_araddr;
(* X_INTERFACE_INFO = "xilinx.com:interface:aximm:1.0 S_AXI ARLEN" *)
input wire [3 : 0] s_axi_arlen;
(* X_INTERFACE_INFO = "xilinx.com:interface:aximm:1.0 S_AXI ARSIZE" *)
input wire [2 : 0] s_axi_arsize;
(* X_INTERFACE_INFO = "xilinx.com:interface:aximm:1.0 S_AXI ARBURST" *)
input wire [1 : 0] s_axi_arburst;
(* X_INTERFACE_INFO = "xilinx.com:interface:aximm:1.0 S_AXI ARLOCK" *)
input wire [1 : 0] s_axi_arlock;
(* X_INTERFACE_INFO = "xilinx.com:interface:aximm:1.0 S_AXI ARCACHE" *)
input wire [3 : 0] s_axi_arcache;
(* X_INTERFACE_INFO = "xilinx.com:interface:aximm:1.0 S_AXI ARPROT" *)
input wire [2 : 0] s_axi_arprot;
(* X_INTERFACE_INFO = "xilinx.com:interface:aximm:1.0 S_AXI ARQOS" *)
input wire [3 : 0] s_axi_arqos;
(* X_INTERFACE_INFO = "xilinx.com:interface:aximm:1.0 S_AXI ARVALID" *)
input wire s_axi_arvalid;
(* X_INTERFACE_INFO = "xilinx.com:interface:aximm:1.0 S_AXI ARREADY" *)
output wire s_axi_arready;
(* X_INTERFACE_INFO = "xilinx.com:interface:aximm:1.0 S_AXI RID" *)
output wire [11 : 0] s_axi_rid;
(* X_INTERFACE_INFO = "xilinx.com:interface:aximm:1.0 S_AXI RDATA" *)
output wire [31 : 0] s_axi_rdata;
(* X_INTERFACE_INFO = "xilinx.com:interface:aximm:1.0 S_AXI RRESP" *)
output wire [1 : 0] s_axi_rresp;
(* X_INTERFACE_INFO = "xilinx.com:interface:aximm:1.0 S_AXI RLAST" *)
output wire s_axi_rlast;
(* X_INTERFACE_INFO = "xilinx.com:interface:aximm:1.0 S_AXI RVALID" *)
output wire s_axi_rvalid;
(* X_INTERFACE_PARAMETER = "XIL_INTERFACENAME S_AXI, DATA_WIDTH 32, PROTOCOL AXI3, FREQ_HZ 147460937, ID_WIDTH 12, ADDR_WIDTH 32, AWUSER_WIDTH 0, ARUSER_WIDTH 0, WUSER_WIDTH 0, RUSER_WIDTH 0, BUSER_WIDTH 0, READ_WRITE_MODE READ_WRITE, HAS_BURST 1, HAS_LOCK 1, HAS_PROT 1, HAS_CACHE 1, HAS_QOS 1, HAS_REGION 0, HAS_WSTRB 1, HAS_BRESP 1, HAS_RRESP 1, SUPPORTS_NARROW_BURST 0, NUM_READ_OUTSTANDING 8, NUM_WRITE_OUTSTANDING 8, MAX_BURST_LENGTH 16, PHASE 0.0, CLK_DOMAIN /clk_wiz_0_clk_out1, NUM_READ_THREADS 4, NUM_WRITE_THREADS 4, \
RUSER_BITS_PER_BYTE 0, WUSER_BITS_PER_BYTE 0, INSERT_VIP 0" *)
(* X_INTERFACE_INFO = "xilinx.com:interface:aximm:1.0 S_AXI RREADY" *)
input wire s_axi_rready;
(* X_INTERFACE_INFO = "xilinx.com:interface:aximm:1.0 M_AXI AWADDR" *)
output wire [31 : 0] m_axi_awaddr;
(* X_INTERFACE_INFO = "xilinx.com:interface:aximm:1.0 M_AXI AWPROT" *)
output wire [2 : 0] m_axi_awprot;
(* X_INTERFACE_INFO = "xilinx.com:interface:aximm:1.0 M_AXI AWVALID" *)
output wire m_axi_awvalid;
(* X_INTERFACE_INFO = "xilinx.com:interface:aximm:1.0 M_AXI AWREADY" *)
input wire m_axi_awready;
(* X_INTERFACE_INFO = "xilinx.com:interface:aximm:1.0 M_AXI WDATA" *)
output wire [31 : 0] m_axi_wdata;
(* X_INTERFACE_INFO = "xilinx.com:interface:aximm:1.0 M_AXI WSTRB" *)
output wire [3 : 0] m_axi_wstrb;
(* X_INTERFACE_INFO = "xilinx.com:interface:aximm:1.0 M_AXI WVALID" *)
output wire m_axi_wvalid;
(* X_INTERFACE_INFO = "xilinx.com:interface:aximm:1.0 M_AXI WREADY" *)
input wire m_axi_wready;
(* X_INTERFACE_INFO = "xilinx.com:interface:aximm:1.0 M_AXI BRESP" *)
input wire [1 : 0] m_axi_bresp;
(* X_INTERFACE_INFO = "xilinx.com:interface:aximm:1.0 M_AXI BVALID" *)
input wire m_axi_bvalid;
(* X_INTERFACE_INFO = "xilinx.com:interface:aximm:1.0 M_AXI BREADY" *)
output wire m_axi_bready;
(* X_INTERFACE_INFO = "xilinx.com:interface:aximm:1.0 M_AXI ARADDR" *)
output wire [31 : 0] m_axi_araddr;
(* X_INTERFACE_INFO = "xilinx.com:interface:aximm:1.0 M_AXI ARPROT" *)
output wire [2 : 0] m_axi_arprot;
(* X_INTERFACE_INFO = "xilinx.com:interface:aximm:1.0 M_AXI ARVALID" *)
output wire m_axi_arvalid;
(* X_INTERFACE_INFO = "xilinx.com:interface:aximm:1.0 M_AXI ARREADY" *)
input wire m_axi_arready;
(* X_INTERFACE_INFO = "xilinx.com:interface:aximm:1.0 M_AXI RDATA" *)
input wire [31 : 0] m_axi_rdata;
(* X_INTERFACE_INFO = "xilinx.com:interface:aximm:1.0 M_AXI RRESP" *)
input wire [1 : 0] m_axi_rresp;
(* X_INTERFACE_INFO = "xilinx.com:interface:aximm:1.0 M_AXI RVALID" *)
input wire m_axi_rvalid;
(* X_INTERFACE_PARAMETER = "XIL_INTERFACENAME M_AXI, DATA_WIDTH 32, PROTOCOL AXI4LITE, FREQ_HZ 147460937, ID_WIDTH 0, ADDR_WIDTH 32, AWUSER_WIDTH 0, ARUSER_WIDTH 0, WUSER_WIDTH 0, RUSER_WIDTH 0, BUSER_WIDTH 0, READ_WRITE_MODE READ_WRITE, HAS_BURST 0, HAS_LOCK 0, HAS_PROT 1, HAS_CACHE 0, HAS_QOS 0, HAS_REGION 0, HAS_WSTRB 1, HAS_BRESP 1, HAS_RRESP 1, SUPPORTS_NARROW_BURST 0, NUM_READ_OUTSTANDING 8, NUM_WRITE_OUTSTANDING 8, MAX_BURST_LENGTH 1, PHASE 0.0, CLK_DOMAIN /clk_wiz_0_clk_out1, NUM_READ_THREADS 4, NUM_WRITE_THREADS 4\
, RUSER_BITS_PER_BYTE 0, WUSER_BITS_PER_BYTE 0, INSERT_VIP 0" *)
(* X_INTERFACE_INFO = "xilinx.com:interface:aximm:1.0 M_AXI RREADY" *)
output wire m_axi_rready;

  axi_protocol_converter_v2_1_19_axi_protocol_converter #(
    .C_FAMILY("zynq"),
    .C_M_AXI_PROTOCOL(2),
    .C_S_AXI_PROTOCOL(1),
    .C_IGNORE_ID(0),
    .C_AXI_ID_WIDTH(12),
    .C_AXI_ADDR_WIDTH(32),
    .C_AXI_DATA_WIDTH(32),
    .C_AXI_SUPPORTS_WRITE(1),
    .C_AXI_SUPPORTS_READ(1),
    .C_AXI_SUPPORTS_USER_SIGNALS(0),
    .C_AXI_AWUSER_WIDTH(1),
    .C_AXI_ARUSER_WIDTH(1),
    .C_AXI_WUSER_WIDTH(1),
    .C_AXI_RUSER_WIDTH(1),
    .C_AXI_BUSER_WIDTH(1),
    .C_TRANSLATION_MODE(2)
  ) inst (
    .aclk(aclk),
    .aresetn(aresetn),
    .s_axi_awid(s_axi_awid),
    .s_axi_awaddr(s_axi_awaddr),
    .s_axi_awlen(s_axi_awlen),
    .s_axi_awsize(s_axi_awsize),
    .s_axi_awburst(s_axi_awburst),
    .s_axi_awlock(s_axi_awlock),
    .s_axi_awcache(s_axi_awcache),
    .s_axi_awprot(s_axi_awprot),
    .s_axi_awregion(4'H0),
    .s_axi_awqos(s_axi_awqos),
    .s_axi_awuser(1'H0),
    .s_axi_awvalid(s_axi_awvalid),
    .s_axi_awready(s_axi_awready),
    .s_axi_wid(s_axi_wid),
    .s_axi_wdata(s_axi_wdata),
    .s_axi_wstrb(s_axi_wstrb),
    .s_axi_wlast(s_axi_wlast),
    .s_axi_wuser(1'H0),
    .s_axi_wvalid(s_axi_wvalid),
    .s_axi_wready(s_axi_wready),
    .s_axi_bid(s_axi_bid),
    .s_axi_bresp(s_axi_bresp),
    .s_axi_buser(),
    .s_axi_bvalid(s_axi_bvalid),
    .s_axi_bready(s_axi_bready),
    .s_axi_arid(s_axi_arid),
    .s_axi_araddr(s_axi_araddr),
    .s_axi_arlen(s_axi_arlen),
    .s_axi_arsize(s_axi_arsize),
    .s_axi_arburst(s_axi_arburst),
    .s_axi_arlock(s_axi_arlock),
    .s_axi_arcache(s_axi_arcache),
    .s_axi_arprot(s_axi_arprot),
    .s_axi_arregion(4'H0),
    .s_axi_arqos(s_axi_arqos),
    .s_axi_aruser(1'H0),
    .s_axi_arvalid(s_axi_arvalid),
    .s_axi_arready(s_axi_arready),
    .s_axi_rid(s_axi_rid),
    .s_axi_rdata(s_axi_rdata),
    .s_axi_rresp(s_axi_rresp),
    .s_axi_rlast(s_axi_rlast),
    .s_axi_ruser(),
    .s_axi_rvalid(s_axi_rvalid),
    .s_axi_rready(s_axi_rready),
    .m_axi_awid(),
    .m_axi_awaddr(m_axi_awaddr),
    .m_axi_awlen(),
    .m_axi_awsize(),
    .m_axi_awburst(),
    .m_axi_awlock(),
    .m_axi_awcache(),
    .m_axi_awprot(m_axi_awprot),
    .m_axi_awregion(),
    .m_axi_awqos(),
    .m_axi_awuser(),
    .m_axi_awvalid(m_axi_awvalid),
    .m_axi_awready(m_axi_awready),
    .m_axi_wid(),
    .m_axi_wdata(m_axi_wdata),
    .m_axi_wstrb(m_axi_wstrb),
    .m_axi_wlast(),
    .m_axi_wuser(),
    .m_axi_wvalid(m_axi_wvalid),
    .m_axi_wready(m_axi_wready),
    .m_axi_bid(12'H000),
    .m_axi_bresp(m_axi_bresp),
    .m_axi_buser(1'H0),
    .m_axi_bvalid(m_axi_bvalid),
    .m_axi_bready(m_axi_bready),
    .m_axi_arid(),
    .m_axi_araddr(m_axi_araddr),
    .m_axi_arlen(),
    .m_axi_arsize(),
    .m_axi_arburst(),
    .m_axi_arlock(),
    .m_axi_arcache(),
    .m_axi_arprot(m_axi_arprot),
    .m_axi_arregion(),
    .m_axi_arqos(),
    .m_axi_aruser(),
    .m_axi_arvalid(m_axi_arvalid),
    .m_axi_arready(m_axi_arready),
    .m_axi_rid(12'H000),
    .m_axi_rdata(m_axi_rdata),
    .m_axi_rresp(m_axi_rresp),
    .m_axi_rlast(1'H1),
    .m_axi_ruser(1'H0),
    .m_axi_rvalid(m_axi_rvalid),
    .m_axi_rready(m_axi_rready)
  );
endmodule
