fpga-theremin/theremin/fpga/theremin_sdk/theremin/src/bitmap_fonts.cpp

/** Standard fonts */
#include "bitmap_fonts.h"

#include <stdint.h>

#if (SCREEN_DX >= 800)
/** Font: XSMALL_FONT   face:Microsoft Sans Serif size:18 weight:400 italic:0 proportional length:2100 bytes*/
ALIGN_4_PREFIX static const uint8_t XSMALL_FONT_data[] ALIGN_4_ATTRIBUTE = {
    0x12, 0x04, 0x20, 0x7e, 0x0f, 0x00, 0x90, 0x01, 0x32, 0x00, 0x34, 0x00, 0x39, 0x00, 0x3c, 0x00, 
    0x41, 0x00, 0x46, 0x00, 0x4d, 0x00, 0x52, 0x00, 0x55, 0x00, 0x5a, 0x00, 0x5f, 0x00, 0x62, 0x00, 
    0x66, 0x00, 0x69, 0x00, 0x6b, 0x00, 0x6d, 0x00, 0x72, 0x00, 0x77, 0x00, 0x7c, 0x00, 0x81, 0x00, 
    0x86, 0x00, 0x8b, 0x00, 0x90, 0x00, 0x95, 0x00, 0x9a, 0x00, 0x9f, 0x00, 0xa4, 0x00, 0xa8, 0x00, 
    0xad, 0x00, 0xb1, 0x00, 0xb4, 0x00, 0xb8, 0x00, 0xbd, 0x00, 0xc6, 0x00, 0xcd, 0x00, 0xd2, 0x00, 
    0xd9, 0x00, 0xe0, 0x00, 0xe5, 0x00, 0xea, 0x00, 0xf1, 0x00, 0xf8, 0x00, 0xfd, 0x00, 0x02, 0x01, 
    0x09, 0x01, 0x0e, 0x01, 0x15, 0x01, 0x1c, 0x01, 0x23, 0x01, 0x2a, 0x01, 0x32, 0x01, 0x39, 0x01, 
    0x3e, 0x01, 0x45, 0x01, 0x4c, 0x01, 0x53, 0x01, 0x5a, 0x01, 0x61, 0x01, 0x68, 0x01, 0x6d, 0x01, 
    0x72, 0x01, 0x77, 0x01, 0x7c, 0x01, 0x7f, 0x01, 0x81, 0x01, 0x83, 0x01, 0x87, 0x01, 0x8c, 0x01, 
    0x90, 0x01, 0x95, 0x01, 0x99, 0x01, 0x9e, 0x01, 0xa3, 0x01, 0xa8, 0x01, 0xad, 0x01, 0xb2, 0x01, 
    0xb7, 0x01, 0xbc, 0x01, 0xc2, 0x01, 0xc6, 0x01, 0xca, 0x01, 0xcf, 0x01, 0xd4, 0x01, 0xd8, 0x01, 
    0xdc, 0x01, 0xe0, 0x01, 0xe4, 0x01, 0xe8, 0x01, 0xee, 0x01, 0xf2, 0x01, 0xf7, 0x01, 0xfb, 0x01, 
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
    0x02, 0x17, 0x08, 0x08, 0x01, 0x07, 0xe0, 0xe0, 0xe0, 0x20, 0x20, 0x40, 0xc0, 0x00, 0x00, 0x00, 
    0x01, 0x12, 0x09, 0x09, 0x01, 0x02, 0xfe, 0xfe, 0x02, 0x17, 0x08, 0x08, 0x01, 0x03, 0xe0, 0xe0, 
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
};
const BitmapFont * XLARGE_FONT = (const BitmapFont *)XLARGE_FONT_data;


#endif
