fpga-theremin/theremin/fpga/theremin_hw/theremin_hw.srcs/sources_1/bd/theremin_hw_bd/ip/theremin_hw_bd_processing_system7_0_0/hdl/verilog/processing_system7_v5_5_processing_system7.v

 
//-----------------------------------------------------------------------------
// processing_system7
// processor sub system wrapper
//-----------------------------------------------------------------------------
//
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
//-----------------------------------------------------------------------------
// Filename:      processing_system7_v5_5_processing_system7.v
// Version:       v1.00.a
// Description:   This is the wrapper file for PSS. 
//-----------------------------------------------------------------------------
// Structure:   This section shows the hierarchical structure of 
//              pss_wrapper.
//
//              --processing_system7_v5_5_processing_system7.v
//                    --PS7.v - Unisim component
//-----------------------------------------------------------------------------
// Author:      SD
//
// History:
//
//  SD      09/20/11      -- First version
// ~~~~~~
// Created the first version v2.00.a
// ^^^^^^
//------------------------------------------------------------------------------
// ^^^^^^
//  SR     11/25/11       -- v3.00.a version
// ~~~~~~~
// Key changes are
// 1. Changed all clock, reset and clktrig ports to be individual
// signals instead of vectors. This is required for modeling of tools.
// 2. Interrupts are now defined as individual signals as well.
// 3. Added Clk buffer logic for FCLK_CLK
// 4. Includes the ACP related changes done
//
// TODO:
// 1. C_NUM_F2P_INTR_INPUTS needs to have control on the
//    number of interrupt ports connected for IRQ_F2P.
// 
//------------------------------------------------------------------------------
// ^^^^^^
//  KP     12/07/11       -- v3.00.a version
// ~~~~~~~
// Key changes are
//  C_NUM_F2P_INTR_INPUTS taken into account for IRQ_F2P
//------------------------------------------------------------------------------
// ^^^^^^
//  NR     12/09/11       -- v3.00.a version
// ~~~~~~~
// Key changes are
//  C_FCLK_CLK0_BUF to C_FCLK_CLK3_BUF parameters were updated 
//  to STRING and fix for CR 640523
//------------------------------------------------------------------------------
// ^^^^^^
//  NR     12/13/11       -- v3.00.a version
// ~~~~~~~
// Key changes are
// Updated IRQ_F2P logic to address CR 641523.
//------------------------------------------------------------------------------
// ^^^^^^
//  NR     02/01/12       -- v3.01.a version
// ~~~~~~~
// Key changes are
// Updated SDIO logic to address CR 636210.
//         |
//         Added C_PS7_SI_REV parameter to track SI Rev
// Removed compress/decompress logic to address CR 642527.
//------------------------------------------------------------------------------
// ^^^^^^
//  NR     02/27/12       -- v3.01.a version
// ~~~~~~~
// Key changes are
// TTC(0,1)_WAVE_OUT and TTC(0,1)_CLK_IN vector signals are made as individual 
// ports as fix for CR 646379
//------------------------------------------------------------------------------
// ^^^^^^
//  NR     03/05/12       -- v3.01.a version
// ~~~~~~~
// Key changes are
// Added/updated compress/decompress logic to address 648393
//------------------------------------------------------------------------------
// ^^^^^^
//  NR     03/14/12       -- v4.00.a version
// ~~~~~~~
// Unused parameters deleted CR 651120
// Addressed CR 651751
//------------------------------------------------------------------------------
// ^^^^^^
//  NR     04/17/12       -- v4.01.a version
// ~~~~~~~
// Added FTM trace buffer functionality
// Added support for ACP AxUSER ports local update
//------------------------------------------------------------------------------
// ^^^^^^
//  VR     05/18/12       -- v4.01.a version
// ~~~~~~~
// Fixed CR#659157
//------------------------------------------------------------------------------
// ^^^^^^
//  VR     07/25/12       -- v4.01.a version
// ~~~~~~~
// Changed S_AXI_HP{1,2}_WACOUNT port's width to 6 from 8 to match unisim model
// Changed fclk_clktrig_gnd width to 4 from 16 to match unisim model
//------------------------------------------------------------------------------
// ^^^^^^
//  VR     11/06/12       -- v5.00 version
// ~~~~~~~
// CR #682573
// Added BIBUF to fixed IO ports and IBUF to fixed input ports
//------------------------------------------------------------------------------
(*POWER= "<PROCESSOR name={system} numA9Cores={2} clockFreq={650} load={0.5} /><MEMORY name={code} memType={DDR3} dataWidth={16} clockFreq={525} readRate={0.5} writeRate={0.5} /><IO interface={GPIO_Bank_1} ioStandard={LVCMOS18} bidis={4} ioBank={Vcco_p1} clockFreq={1} usageRate={0.5} /><IO interface={GPIO_Bank_0} ioStandard={LVCMOS33} bidis={13} ioBank={Vcco_p0} clockFreq={1} usageRate={0.5} /><IO interface={UART} ioStandard={LVCMOS33} bidis={2} ioBank={Vcco_p0} clockFreq={100.000000} usageRate={0.5} /><IO interface={SD} ioStandard={LVCMOS18} bidis={7} ioBank={Vcco_p1} clockFreq={100.000000} usageRate={0.5} /><IO interface={USB} ioStandard={LVCMOS18} bidis={12} ioBank={Vcco_p1} clockFreq={60} usageRate={0.5} /><IO interface={GigE} ioStandard={LVCMOS18} bidis={14} ioBank={Vcco_p1} clockFreq={125.000000} usageRate={0.5} /><PLL domain={Processor} vco={1300.000} /><PLL domain={Memory} vco={1050.000} /><PLL domain={IO} vco={1000.000} /><AXI interface={S_AXI_HP0} dataWidth={32} clockFreq={147} usageRate={0.5} /><AXI interface={M_AXI_GP0} dataWidth={32} clockFreq={147} usageRate={0.5} />/>" *)
(* CORE_GENERATION_INFO = "processing_system7_v5.5 ,processing_system7_v5.5_user_configuration,{ PCW_UIPARAM_DDR_FREQ_MHZ=525, PCW_UIPARAM_DDR_BANK_ADDR_COUNT=3, PCW_UIPARAM_DDR_ROW_ADDR_COUNT=15, PCW_UIPARAM_DDR_COL_ADDR_COUNT=10, PCW_UIPARAM_DDR_CL=7, PCW_UIPARAM_DDR_CWL=6, PCW_UIPARAM_DDR_T_RCD=7, PCW_UIPARAM_DDR_T_RP=7, PCW_UIPARAM_DDR_T_RC=48.75, PCW_UIPARAM_DDR_T_RAS_MIN=35.0, PCW_UIPARAM_DDR_T_FAW=40.0, PCW_UIPARAM_DDR_AL=0, PCW_UIPARAM_DDR_DQS_TO_CLK_DELAY_0=0.040, PCW_UIPARAM_DDR_DQS_TO_CLK_DELAY_1=0.058, PCW_UIPARAM_DDR_DQS_TO_CLK_DELAY_2=-0.009, PCW_UIPARAM_DDR_DQS_TO_CLK_DELAY_3=-0.033, PCW_UIPARAM_DDR_BOARD_DELAY0=0.223, PCW_UIPARAM_DDR_BOARD_DELAY1=0.212, PCW_UIPARAM_DDR_BOARD_DELAY2=0.085, PCW_UIPARAM_DDR_BOARD_DELAY3=0.092, PCW_UIPARAM_DDR_DQS_0_LENGTH_MM=15.6, PCW_UIPARAM_DDR_DQS_1_LENGTH_MM=18.8, PCW_UIPARAM_DDR_DQS_2_LENGTH_MM=0, PCW_UIPARAM_DDR_DQS_3_LENGTH_MM=0, PCW_UIPARAM_DDR_DQ_0_LENGTH_MM=16.5, PCW_UIPARAM_DDR_DQ_1_LENGTH_MM=18, PCW_UIPARAM_DDR_DQ_2_LENGTH_MM=0, PCW_UIPARAM_DDR_DQ_3_LENGTH_MM=0, PCW_UIPARAM_DDR_CLOCK_0_LENGTH_MM=15.8, PCW_UIPARAM_DDR_CLOCK_1_LENGTH_MM=15.8, PCW_UIPARAM_DDR_CLOCK_2_LENGTH_MM=0, PCW_UIPARAM_DDR_CLOCK_3_LENGTH_MM=0, PCW_UIPARAM_DDR_DQS_0_PACKAGE_LENGTH=105.056, PCW_UIPARAM_DDR_DQS_1_PACKAGE_LENGTH=66.904, PCW_UIPARAM_DDR_DQS_2_PACKAGE_LENGTH=89.1715, PCW_UIPARAM_DDR_DQS_3_PACKAGE_LENGTH=113.63, PCW_UIPARAM_DDR_DQ_0_PACKAGE_LENGTH=98.503, PCW_UIPARAM_DDR_DQ_1_PACKAGE_LENGTH=68.5855, PCW_UIPARAM_DDR_DQ_2_PACKAGE_LENGTH=90.295, PCW_UIPARAM_DDR_DQ_3_PACKAGE_LENGTH=103.977, PCW_UIPARAM_DDR_CLOCK_0_PACKAGE_LENGTH=80.4535, PCW_UIPARAM_DDR_CLOCK_1_PACKAGE_LENGTH=80.4535, PCW_UIPARAM_DDR_CLOCK_2_PACKAGE_LENGTH=80.4535, PCW_UIPARAM_DDR_CLOCK_3_PACKAGE_LENGTH=80.4535, PCW_UIPARAM_DDR_DQS_0_PROPOGATION_DELAY=160, PCW_UIPARAM_DDR_DQS_1_PROPOGATION_DELAY=160, PCW_UIPARAM_DDR_DQS_2_PROPOGATION_DELAY=160, PCW_UIPARAM_DDR_DQS_3_PROPOGATION_DELAY=160, PCW_UIPARAM_DDR_DQ_0_PROPOGATION_DELAY=160, PCW_UIPARAM_DDR_DQ_1_PROPOGATION_DELAY=160\
, PCW_UIPARAM_DDR_DQ_2_PROPOGATION_DELAY=160, PCW_UIPARAM_DDR_DQ_3_PROPOGATION_DELAY=160, PCW_UIPARAM_DDR_CLOCK_0_PROPOGATION_DELAY=160, PCW_UIPARAM_DDR_CLOCK_1_PROPOGATION_DELAY=160, PCW_UIPARAM_DDR_CLOCK_2_PROPOGATION_DELAY=160, PCW_UIPARAM_DDR_CLOCK_3_PROPOGATION_DELAY=160, PCW_CRYSTAL_PERIPHERAL_FREQMHZ=50, PCW_APU_PERIPHERAL_FREQMHZ=650, PCW_DCI_PERIPHERAL_FREQMHZ=10.159, PCW_QSPI_PERIPHERAL_FREQMHZ=200, PCW_SMC_PERIPHERAL_FREQMHZ=100, PCW_USB0_PERIPHERAL_FREQMHZ=60, PCW_USB1_PERIPHERAL_FREQMHZ=60, PCW_SDIO_PERIPHERAL_FREQMHZ=100, PCW_UART_PERIPHERAL_FREQMHZ=100, PCW_SPI_PERIPHERAL_FREQMHZ=166.666666, PCW_CAN_PERIPHERAL_FREQMHZ=100, PCW_CAN0_PERIPHERAL_FREQMHZ=-1, PCW_CAN1_PERIPHERAL_FREQMHZ=-1, PCW_WDT_PERIPHERAL_FREQMHZ=133.333333, PCW_TTC_PERIPHERAL_FREQMHZ=50, PCW_TTC0_CLK0_PERIPHERAL_FREQMHZ=133.333333, PCW_TTC0_CLK1_PERIPHERAL_FREQMHZ=133.333333, PCW_TTC0_CLK2_PERIPHERAL_FREQMHZ=133.333333, PCW_TTC1_CLK0_PERIPHERAL_FREQMHZ=133.333333, PCW_TTC1_CLK1_PERIPHERAL_FREQMHZ=133.333333, PCW_TTC1_CLK2_PERIPHERAL_FREQMHZ=133.333333, PCW_PCAP_PERIPHERAL_FREQMHZ=200, PCW_TPIU_PERIPHERAL_FREQMHZ=200, PCW_FPGA0_PERIPHERAL_FREQMHZ=100, PCW_FPGA1_PERIPHERAL_FREQMHZ=50, PCW_FPGA2_PERIPHERAL_FREQMHZ=50, PCW_FPGA3_PERIPHERAL_FREQMHZ=50, PCW_OVERRIDE_BASIC_CLOCK=0, PCW_ARMPLL_CTRL_FBDIV=26, PCW_IOPLL_CTRL_FBDIV=20, PCW_DDRPLL_CTRL_FBDIV=21, PCW_CPU_CPU_PLL_FREQMHZ=1300.000, PCW_IO_IO_PLL_FREQMHZ=1000.000, PCW_DDR_DDR_PLL_FREQMHZ=1050.000, PCW_USE_M_AXI_GP0=1, PCW_USE_M_AXI_GP1=0, PCW_USE_S_AXI_GP0=0, PCW_USE_S_AXI_GP1=0, PCW_USE_S_AXI_ACP=0, PCW_USE_S_AXI_HP0=1, PCW_USE_S_AXI_HP1=0, PCW_USE_S_AXI_HP2=0, PCW_USE_S_AXI_HP3=0, PCW_M_AXI_GP0_FREQMHZ=147\
, PCW_M_AXI_GP1_FREQMHZ=10, PCW_S_AXI_GP0_FREQMHZ=10, PCW_S_AXI_GP1_FREQMHZ=10, PCW_S_AXI_ACP_FREQMHZ=10, PCW_S_AXI_HP0_FREQMHZ=147, PCW_S_AXI_HP1_FREQMHZ=10, PCW_S_AXI_HP2_FREQMHZ=10, PCW_S_AXI_HP3_FREQMHZ=10, PCW_USE_CROSS_TRIGGER=0, PCW_UART0_BAUD_RATE=921600, PCW_UART1_BAUD_RATE=115200, PCW_S_AXI_HP0_DATA_WIDTH=32, PCW_S_AXI_HP1_DATA_WIDTH=64, PCW_S_AXI_HP2_DATA_WIDTH=64, PCW_S_AXI_HP3_DATA_WIDTH=64, PCW_IRQ_F2P_MODE=DIRECT, PCW_PRESET_BANK0_VOLTAGE=LVCMOS 3.3V, PCW_PRESET_BANK1_VOLTAGE=LVCMOS 1.8V, PCW_UIPARAM_DDR_ENABLE=1, PCW_UIPARAM_DDR_ADV_ENABLE=0, PCW_UIPARAM_DDR_MEMORY_TYPE=DDR 3, PCW_UIPARAM_DDR_ECC=Disabled, PCW_UIPARAM_DDR_BUS_WIDTH=16 Bit, PCW_UIPARAM_DDR_BL=8, PCW_UIPARAM_DDR_HIGH_TEMP=Normal (0-85), PCW_UIPARAM_DDR_PARTNO=MT41K256M16 RE-125, PCW_UIPARAM_DDR_DRAM_WIDTH=16 Bits, PCW_UIPARAM_DDR_DEVICE_CAPACITY=4096 MBits, PCW_UIPARAM_DDR_SPEED_BIN=DDR3_1066F, PCW_UIPARAM_DDR_TRAIN_WRITE_LEVEL=1, PCW_UIPARAM_DDR_TRAIN_READ_GATE=1, PCW_UIPARAM_DDR_TRAIN_DATA_EYE=1, PCW_UIPARAM_DDR_CLOCK_STOP_EN=0, PCW_UIPARAM_DDR_USE_INTERNAL_VREF=0, PCW_DDR_PORT0_HPR_ENABLE=0, PCW_DDR_PORT1_HPR_ENABLE=0, PCW_DDR_PORT2_HPR_ENABLE=0, PCW_DDR_PORT3_HPR_ENABLE=0, PCW_DDR_HPRLPR_QUEUE_PARTITION=HPR(0)/LPR(32), PCW_DDR_LPR_TO_CRITICAL_PRIORITY_LEVEL=2, PCW_DDR_HPR_TO_CRITICAL_PRIORITY_LEVEL=15, PCW_DDR_WRITE_TO_CRITICAL_PRIORITY_LEVEL=2, PCW_NAND_PERIPHERAL_ENABLE=0, PCW_NAND_GRP_D8_ENABLE=0, PCW_NOR_PERIPHERAL_ENABLE=0, PCW_NOR_GRP_A25_ENABLE=0, PCW_NOR_GRP_CS0_ENABLE=0, PCW_NOR_GRP_SRAM_CS0_ENABLE=0, PCW_NOR_GRP_CS1_ENABLE=0, PCW_NOR_GRP_SRAM_CS1_ENABLE=0\
, PCW_NOR_GRP_SRAM_INT_ENABLE=0, PCW_QSPI_PERIPHERAL_ENABLE=0, PCW_QSPI_GRP_SINGLE_SS_ENABLE=0, PCW_QSPI_GRP_SS1_ENABLE=0, PCW_QSPI_GRP_IO1_ENABLE=0, PCW_QSPI_GRP_FBCLK_ENABLE=0, PCW_QSPI_INTERNAL_HIGHADDRESS=0xFCFFFFFF, PCW_ENET0_PERIPHERAL_ENABLE=1, PCW_ENET0_ENET0_IO=MIO 16 .. 27, PCW_ENET0_GRP_MDIO_ENABLE=1, PCW_ENET0_RESET_ENABLE=1, PCW_ENET0_RESET_IO=MIO 9, PCW_ENET1_PERIPHERAL_ENABLE=0, PCW_ENET1_GRP_MDIO_ENABLE=0, PCW_ENET1_RESET_ENABLE=0, PCW_SD0_PERIPHERAL_ENABLE=1, PCW_SD0_SD0_IO=MIO 40 .. 45, PCW_SD0_GRP_CD_ENABLE=1, PCW_SD0_GRP_CD_IO=MIO 47, PCW_SD0_GRP_WP_ENABLE=0, PCW_SD0_GRP_POW_ENABLE=0, PCW_SD1_PERIPHERAL_ENABLE=0, PCW_SD1_GRP_CD_ENABLE=0, PCW_SD1_GRP_WP_ENABLE=0, PCW_SD1_GRP_POW_ENABLE=0, PCW_UART0_PERIPHERAL_ENABLE=1, PCW_UART0_UART0_IO=MIO 14 .. 15, PCW_UART0_GRP_FULL_ENABLE=0, PCW_UART1_PERIPHERAL_ENABLE=0, PCW_UART1_GRP_FULL_ENABLE=0, PCW_SPI0_PERIPHERAL_ENABLE=0, PCW_SPI0_GRP_SS0_ENABLE=0, PCW_SPI0_GRP_SS1_ENABLE=0, PCW_SPI0_GRP_SS2_ENABLE=0, PCW_SPI1_PERIPHERAL_ENABLE=0, PCW_SPI1_GRP_SS0_ENABLE=0, PCW_SPI1_GRP_SS1_ENABLE=0, PCW_SPI1_GRP_SS2_ENABLE=0, PCW_CAN0_PERIPHERAL_ENABLE=0, PCW_CAN0_GRP_CLK_ENABLE=0, PCW_CAN1_PERIPHERAL_ENABLE=0, PCW_CAN1_GRP_CLK_ENABLE=0, PCW_TRACE_PERIPHERAL_ENABLE=0, PCW_TRACE_GRP_2BIT_ENABLE=0, PCW_TRACE_GRP_4BIT_ENABLE=0, PCW_TRACE_GRP_8BIT_ENABLE=0, PCW_TRACE_GRP_16BIT_ENABLE=0, PCW_TRACE_GRP_32BIT_ENABLE=0, PCW_WDT_PERIPHERAL_ENABLE=0, PCW_TTC0_PERIPHERAL_ENABLE=0\
, PCW_TTC1_PERIPHERAL_ENABLE=0, PCW_PJTAG_PERIPHERAL_ENABLE=0, PCW_USB0_PERIPHERAL_ENABLE=1, PCW_USB0_USB0_IO=MIO 28 .. 39, PCW_USB0_RESET_ENABLE=1, PCW_USB0_RESET_IO=MIO 46, PCW_USB1_PERIPHERAL_ENABLE=0, PCW_USB1_RESET_ENABLE=0, PCW_I2C0_PERIPHERAL_ENABLE=0, PCW_I2C0_GRP_INT_ENABLE=0, PCW_I2C0_RESET_ENABLE=0, PCW_I2C1_PERIPHERAL_ENABLE=0, PCW_I2C1_GRP_INT_ENABLE=0, PCW_I2C1_RESET_ENABLE=0, PCW_GPIO_PERIPHERAL_ENABLE=0, PCW_GPIO_MIO_GPIO_ENABLE=1, PCW_GPIO_MIO_GPIO_IO=MIO, PCW_GPIO_EMIO_GPIO_ENABLE=0, PCW_APU_CLK_RATIO_ENABLE=6:2:1, PCW_ENET0_PERIPHERAL_FREQMHZ=1000 Mbps, PCW_ENET1_PERIPHERAL_FREQMHZ=1000 Mbps, PCW_CPU_PERIPHERAL_CLKSRC=ARM PLL, PCW_DDR_PERIPHERAL_CLKSRC=DDR PLL, PCW_SMC_PERIPHERAL_CLKSRC=IO PLL, PCW_QSPI_PERIPHERAL_CLKSRC=IO PLL, PCW_SDIO_PERIPHERAL_CLKSRC=IO PLL, PCW_UART_PERIPHERAL_CLKSRC=IO PLL, PCW_SPI_PERIPHERAL_CLKSRC=IO PLL, PCW_CAN_PERIPHERAL_CLKSRC=IO PLL, PCW_FCLK0_PERIPHERAL_CLKSRC=IO PLL, PCW_FCLK1_PERIPHERAL_CLKSRC=IO PLL, PCW_FCLK2_PERIPHERAL_CLKSRC=IO PLL, PCW_FCLK3_PERIPHERAL_CLKSRC=IO PLL, PCW_ENET0_PERIPHERAL_CLKSRC=IO PLL, PCW_ENET1_PERIPHERAL_CLKSRC=IO PLL, PCW_CAN0_PERIPHERAL_CLKSRC=External, PCW_CAN1_PERIPHERAL_CLKSRC=External, PCW_TPIU_PERIPHERAL_CLKSRC=External, PCW_TTC0_CLK0_PERIPHERAL_CLKSRC=CPU_1X, PCW_TTC0_CLK1_PERIPHERAL_CLKSRC=CPU_1X, PCW_TTC0_CLK2_PERIPHERAL_CLKSRC=CPU_1X, PCW_TTC1_CLK0_PERIPHERAL_CLKSRC=CPU_1X, PCW_TTC1_CLK1_PERIPHERAL_CLKSRC=CPU_1X, PCW_TTC1_CLK2_PERIPHERAL_CLKSRC=CPU_1X, PCW_WDT_PERIPHERAL_CLKSRC=CPU_1X, PCW_DCI_PERIPHERAL_CLKSRC=DDR PLL, PCW_PCAP_PERIPHERAL_CLKSRC=IO PLL, PCW_USB_RESET_POLARITY=Active Low, PCW_ENET_RESET_POLARITY=Active Low, PCW_I2C_RESET_POLARITY=Active Low\
, PCW_FPGA_FCLK0_ENABLE=1, PCW_FPGA_FCLK1_ENABLE=0, PCW_FPGA_FCLK2_ENABLE=0, PCW_FPGA_FCLK3_ENABLE=0, PCW_NOR_SRAM_CS0_T_TR=1, PCW_NOR_SRAM_CS0_T_PC=1, PCW_NOR_SRAM_CS0_T_WP=1, PCW_NOR_SRAM_CS0_T_CEOE=1, PCW_NOR_SRAM_CS0_T_WC=11, PCW_NOR_SRAM_CS0_T_RC=11, PCW_NOR_SRAM_CS0_WE_TIME=0, PCW_NOR_SRAM_CS1_T_TR=1, PCW_NOR_SRAM_CS1_T_PC=1, PCW_NOR_SRAM_CS1_T_WP=1, PCW_NOR_SRAM_CS1_T_CEOE=1, PCW_NOR_SRAM_CS1_T_WC=11, PCW_NOR_SRAM_CS1_T_RC=11, PCW_NOR_SRAM_CS1_WE_TIME=0, PCW_NOR_CS0_T_TR=1, PCW_NOR_CS0_T_PC=1, PCW_NOR_CS0_T_WP=1, PCW_NOR_CS0_T_CEOE=1, PCW_NOR_CS0_T_WC=11, PCW_NOR_CS0_T_RC=11, PCW_NOR_CS0_WE_TIME=0, PCW_NOR_CS1_T_TR=1, PCW_NOR_CS1_T_PC=1, PCW_NOR_CS1_T_WP=1, PCW_NOR_CS1_T_CEOE=1, PCW_NOR_CS1_T_WC=11, PCW_NOR_CS1_T_RC=11, PCW_NOR_CS1_WE_TIME=0, PCW_NAND_CYCLES_T_RR=1, PCW_NAND_CYCLES_T_AR=1, PCW_NAND_CYCLES_T_CLR=1, PCW_NAND_CYCLES_T_WP=1, PCW_NAND_CYCLES_T_REA=1, PCW_NAND_CYCLES_T_WC=11, PCW_NAND_CYCLES_T_RC=11 }" *)  
(* HW_HANDOFF = "theremin_hw_bd_processing_system7_0_0.hwdef" *)  

module processing_system7_v5_5_processing_system7

#(
  parameter integer C_USE_DEFAULT_ACP_USER_VAL = 1,
  parameter integer C_S_AXI_ACP_ARUSER_VAL = 31,
  parameter integer C_S_AXI_ACP_AWUSER_VAL = 31,
  parameter integer C_M_AXI_GP0_THREAD_ID_WIDTH = 12,
  parameter integer C_M_AXI_GP1_THREAD_ID_WIDTH = 12, 
  parameter integer C_M_AXI_GP0_ENABLE_STATIC_REMAP = 1,
  parameter integer C_M_AXI_GP1_ENABLE_STATIC_REMAP = 1, 
  parameter integer C_M_AXI_GP0_ID_WIDTH = 12,
  parameter integer C_M_AXI_GP1_ID_WIDTH = 12,
  parameter integer C_S_AXI_GP0_ID_WIDTH = 6,
  parameter integer C_S_AXI_GP1_ID_WIDTH = 6,
  parameter integer C_S_AXI_HP0_ID_WIDTH = 6,
  parameter integer C_S_AXI_HP1_ID_WIDTH = 6,
  parameter integer C_S_AXI_HP2_ID_WIDTH = 6,
  parameter integer C_S_AXI_HP3_ID_WIDTH = 6,
  parameter integer C_S_AXI_ACP_ID_WIDTH = 3,
  parameter integer C_S_AXI_HP0_DATA_WIDTH = 64,
  parameter integer C_S_AXI_HP1_DATA_WIDTH = 64,
  parameter integer C_S_AXI_HP2_DATA_WIDTH = 64,
  parameter integer C_S_AXI_HP3_DATA_WIDTH = 64,
  parameter integer C_INCLUDE_ACP_TRANS_CHECK = 0,
  parameter integer C_NUM_F2P_INTR_INPUTS = 1,
  parameter         C_FCLK_CLK0_BUF = "TRUE",
  parameter         C_FCLK_CLK1_BUF = "TRUE",
  parameter         C_FCLK_CLK2_BUF = "TRUE",
  parameter         C_FCLK_CLK3_BUF = "TRUE",
  parameter integer C_EMIO_GPIO_WIDTH = 64,
  parameter integer C_INCLUDE_TRACE_BUFFER = 0,
  parameter integer C_TRACE_BUFFER_FIFO_SIZE = 128,
  parameter integer C_TRACE_BUFFER_CLOCK_DELAY = 12,
  parameter integer USE_TRACE_DATA_EDGE_DETECTOR = 0,
  parameter integer C_TRACE_PIPELINE_WIDTH = 8,
  parameter         C_PS7_SI_REV = "PRODUCTION",
  parameter integer C_EN_EMIO_ENET0 = 0,
  parameter integer C_EN_EMIO_ENET1 = 0,
  parameter integer C_EN_EMIO_TRACE = 0,
  parameter integer C_DQ_WIDTH = 32,
  parameter integer C_DQS_WIDTH = 4,
  parameter integer C_DM_WIDTH = 4,
  parameter integer C_MIO_PRIMITIVE = 54,
  parameter	    C_PACKAGE_NAME = "clg484",
  parameter C_IRQ_F2P_MODE = "DIRECT",
  parameter C_TRACE_INTERNAL_WIDTH = 32,
  parameter integer C_EN_EMIO_PJTAG = 0,
  
  // Enable and disable AFI Secure transaction 
  parameter C_USE_AXI_NONSECURE = 0,
  
  //parameters for HP enable ports 
  parameter C_USE_S_AXI_HP0 = 0,
  parameter C_USE_S_AXI_HP1 = 0,
  parameter C_USE_S_AXI_HP2 = 0,
  parameter C_USE_S_AXI_HP3 = 0,
  
  //parameters for GP and ACP enable ports */
  parameter C_USE_M_AXI_GP0 = 0,
  parameter C_USE_M_AXI_GP1 = 0,
  parameter C_USE_S_AXI_GP0 = 0,
  parameter C_USE_S_AXI_GP1 = 0,
  parameter C_USE_S_AXI_ACP = 0,
  parameter C_GP0_EN_MODIFIABLE_TXN=0,
  parameter C_GP1_EN_MODIFIABLE_TXN=0
   
)
(
  //FMIO =========================================
  
  //FMIO CAN0
  output          CAN0_PHY_TX,
  input           CAN0_PHY_RX,

  //FMIO CAN1
  output          CAN1_PHY_TX,  
  input           CAN1_PHY_RX,
  
  //FMIO ENET0
  output  reg     ENET0_GMII_TX_EN = 'b0,
  output  reg     ENET0_GMII_TX_ER = 'b0,
  output          ENET0_MDIO_MDC,
  output          ENET0_MDIO_O,
  output          ENET0_MDIO_T,
  output          ENET0_PTP_DELAY_REQ_RX,
  output          ENET0_PTP_DELAY_REQ_TX,
  output          ENET0_PTP_PDELAY_REQ_RX,
  output          ENET0_PTP_PDELAY_REQ_TX,
  output          ENET0_PTP_PDELAY_RESP_RX,
  output          ENET0_PTP_PDELAY_RESP_TX,
  output          ENET0_PTP_SYNC_FRAME_RX,
  output          ENET0_PTP_SYNC_FRAME_TX,
  output          ENET0_SOF_RX,
  output          ENET0_SOF_TX,
  
  
  output  reg [7:0]    ENET0_GMII_TXD,  

  
  input           ENET0_GMII_COL,
  input           ENET0_GMII_CRS,
  input           ENET0_GMII_RX_CLK,
  input           ENET0_GMII_RX_DV,
  input           ENET0_GMII_RX_ER,
  input           ENET0_GMII_TX_CLK,
  input           ENET0_MDIO_I,
  input           ENET0_EXT_INTIN,
  input [7:0]     ENET0_GMII_RXD,  

  //FMIO ENET1
  output   reg    ENET1_GMII_TX_EN = 'b0,
  output   reg    ENET1_GMII_TX_ER = 'b0,
  output          ENET1_MDIO_MDC,
  output          ENET1_MDIO_O,
  output          ENET1_MDIO_T,
  output          ENET1_PTP_DELAY_REQ_RX,
  output          ENET1_PTP_DELAY_REQ_TX,
  output          ENET1_PTP_PDELAY_REQ_RX,
  output          ENET1_PTP_PDELAY_REQ_TX,
  output          ENET1_PTP_PDELAY_RESP_RX,
  output          ENET1_PTP_PDELAY_RESP_TX,
  output          ENET1_PTP_SYNC_FRAME_RX,
  output          ENET1_PTP_SYNC_FRAME_TX,
  output          ENET1_SOF_RX,
  output          ENET1_SOF_TX,
  output reg [7:0]    ENET1_GMII_TXD,  

  input          ENET1_GMII_COL,
  input          ENET1_GMII_CRS,
  input          ENET1_GMII_RX_CLK,
  input          ENET1_GMII_RX_DV,
  input          ENET1_GMII_RX_ER,
  input          ENET1_GMII_TX_CLK,
  input          ENET1_MDIO_I,
  input          ENET1_EXT_INTIN,  
  input [7:0]    ENET1_GMII_RXD,
  
  //FMIO GPIO
  input    [(C_EMIO_GPIO_WIDTH-1):0] GPIO_I,
  output   [(C_EMIO_GPIO_WIDTH-1):0] GPIO_O,
  output   [(C_EMIO_GPIO_WIDTH-1):0] GPIO_T,  
  
  //FMIO I2C0
  input           I2C0_SDA_I,
  output          I2C0_SDA_O,
  output          I2C0_SDA_T,
  input           I2C0_SCL_I,
  output          I2C0_SCL_O,
  output          I2C0_SCL_T,

  //FMIO I2C1
  input           I2C1_SDA_I,
  output          I2C1_SDA_O,
  output          I2C1_SDA_T,
  input           I2C1_SCL_I,
  output          I2C1_SCL_O,
  output          I2C1_SCL_T,
  
  //FMIO PJTAG
  input           PJTAG_TCK,
  input           PJTAG_TMS,
  input           PJTAG_TDI,
  output          PJTAG_TDO,

  
  //FMIO SDIO0
  output          SDIO0_CLK,
  input           SDIO0_CLK_FB,
  output          SDIO0_CMD_O,
  input           SDIO0_CMD_I,
  output          SDIO0_CMD_T,
  input     [3:0] SDIO0_DATA_I,
  output    [3:0] SDIO0_DATA_O,
  output    [3:0] SDIO0_DATA_T,
  output          SDIO0_LED,
  input           SDIO0_CDN,
  input           SDIO0_WP,  
  output          SDIO0_BUSPOW,
  output    [2:0] SDIO0_BUSVOLT,

  //FMIO SDIO1
  output          SDIO1_CLK,
  input           SDIO1_CLK_FB,
  output          SDIO1_CMD_O,
  input           SDIO1_CMD_I,
  output          SDIO1_CMD_T,
  input     [3:0] SDIO1_DATA_I,
  output    [3:0] SDIO1_DATA_O,
  output    [3:0] SDIO1_DATA_T,  
  output          SDIO1_LED,
  input           SDIO1_CDN,  
  input           SDIO1_WP,
  output          SDIO1_BUSPOW,  
  output    [2:0] SDIO1_BUSVOLT,

  //FMIO SPI0
  input           SPI0_SCLK_I,
  output          SPI0_SCLK_O,
  output          SPI0_SCLK_T,
  input           SPI0_MOSI_I,
  output          SPI0_MOSI_O,
  output          SPI0_MOSI_T,
  input           SPI0_MISO_I,
  output          SPI0_MISO_O,
  output          SPI0_MISO_T,
  input           SPI0_SS_I,
  output          SPI0_SS_O,
  output          SPI0_SS1_O,
  output          SPI0_SS2_O,
  output          SPI0_SS_T,

  //FMIO SPI1
  input           SPI1_SCLK_I,
  output          SPI1_SCLK_O,
  output          SPI1_SCLK_T,
  input           SPI1_MOSI_I,
  output          SPI1_MOSI_O,
  output          SPI1_MOSI_T,
  input           SPI1_MISO_I,
  output          SPI1_MISO_O,
  output          SPI1_MISO_T,
  input           SPI1_SS_I,
  output          SPI1_SS_O,
  output          SPI1_SS1_O,
  output          SPI1_SS2_O,  
  output          SPI1_SS_T,

  //FMIO UART0
  output          UART0_DTRN,
  output          UART0_RTSN,  
  output          UART0_TX,
  input           UART0_CTSN,
  input           UART0_DCDN,
  input           UART0_DSRN,
  input           UART0_RIN,  
  input           UART0_RX,

  //FMIO UART1
  output          UART1_DTRN,
  output          UART1_RTSN,  
  output          UART1_TX,
  input           UART1_CTSN,
  input           UART1_DCDN,
  input           UART1_DSRN,
  input           UART1_RIN,  
  input           UART1_RX,

  //FMIO TTC0
  output    		TTC0_WAVE0_OUT,
  output    		TTC0_WAVE1_OUT,
  output    		TTC0_WAVE2_OUT,
  input     		TTC0_CLK0_IN,
  input     		TTC0_CLK1_IN,
  input     		TTC0_CLK2_IN,

  //FMIO TTC1
  output    		TTC1_WAVE0_OUT,
  output    		TTC1_WAVE1_OUT,
  output    		TTC1_WAVE2_OUT,
  input     		TTC1_CLK0_IN,
  input     		TTC1_CLK1_IN,
  input     		TTC1_CLK2_IN,

  //WDT
  input           WDT_CLK_IN,
  output          WDT_RST_OUT,

  //FTPORT
  input           TRACE_CLK,
  output          TRACE_CTL,
  output   [(C_TRACE_INTERNAL_WIDTH)-1:0] TRACE_DATA,
  output   reg		  TRACE_CLK_OUT,
  
  // USB
  output   [1:0]  USB0_PORT_INDCTL,
  output          USB0_VBUS_PWRSELECT,
  input           USB0_VBUS_PWRFAULT,

  output   [1:0]  USB1_PORT_INDCTL,
  output          USB1_VBUS_PWRSELECT,
  input           USB1_VBUS_PWRFAULT,
  
  input           SRAM_INTIN,

  //AIO ===================================================

  //M_AXI_GP0
  
  // -- Output
  
  output M_AXI_GP0_ARESETN,
  output M_AXI_GP0_ARVALID,
  output M_AXI_GP0_AWVALID,
  output M_AXI_GP0_BREADY,
  output M_AXI_GP0_RREADY,
  output M_AXI_GP0_WLAST,
  output M_AXI_GP0_WVALID,
  output [(C_M_AXI_GP0_THREAD_ID_WIDTH - 1):0] M_AXI_GP0_ARID,
  output [(C_M_AXI_GP0_THREAD_ID_WIDTH - 1):0] M_AXI_GP0_AWID,
  output [(C_M_AXI_GP0_THREAD_ID_WIDTH - 1):0] M_AXI_GP0_WID,
  output [1:0] M_AXI_GP0_ARBURST,
  output [1:0] M_AXI_GP0_ARLOCK,
  output [2:0] M_AXI_GP0_ARSIZE,
  output [1:0] M_AXI_GP0_AWBURST,
  output [1:0] M_AXI_GP0_AWLOCK,
  output [2:0] M_AXI_GP0_AWSIZE,
  output [2:0] M_AXI_GP0_ARPROT,
  output [2:0] M_AXI_GP0_AWPROT,
  output [31:0] M_AXI_GP0_ARADDR,
  output [31:0] M_AXI_GP0_AWADDR,
  output [31:0] M_AXI_GP0_WDATA,
  output [3:0] M_AXI_GP0_ARCACHE,
  output [3:0] M_AXI_GP0_ARLEN,
  output [3:0] M_AXI_GP0_ARQOS,
  output [3:0] M_AXI_GP0_AWCACHE,
  output [3:0] M_AXI_GP0_AWLEN,
  output [3:0] M_AXI_GP0_AWQOS,
  output [3:0] M_AXI_GP0_WSTRB, 
  
  // -- Input  
  
  input M_AXI_GP0_ACLK,
  input M_AXI_GP0_ARREADY,
  input M_AXI_GP0_AWREADY,
  input M_AXI_GP0_BVALID,
  input M_AXI_GP0_RLAST,
  input M_AXI_GP0_RVALID,
  input M_AXI_GP0_WREADY,
  input [(C_M_AXI_GP0_THREAD_ID_WIDTH - 1):0] M_AXI_GP0_BID,
  input [(C_M_AXI_GP0_THREAD_ID_WIDTH - 1):0] M_AXI_GP0_RID,
  input [1:0] M_AXI_GP0_BRESP,
  input [1:0] M_AXI_GP0_RRESP,
  input [31:0] M_AXI_GP0_RDATA,  


  //M_AXI_GP1
  
  // -- Output

  output M_AXI_GP1_ARESETN,
  output M_AXI_GP1_ARVALID,
  output M_AXI_GP1_AWVALID,
  output M_AXI_GP1_BREADY,
  output M_AXI_GP1_RREADY,
  output M_AXI_GP1_WLAST,
  output M_AXI_GP1_WVALID,
  output [(C_M_AXI_GP1_THREAD_ID_WIDTH - 1):0] M_AXI_GP1_ARID,
  output [(C_M_AXI_GP1_THREAD_ID_WIDTH - 1):0] M_AXI_GP1_AWID,
  output [(C_M_AXI_GP1_THREAD_ID_WIDTH - 1):0] M_AXI_GP1_WID,
  output [1:0] M_AXI_GP1_ARBURST,
  output [1:0] M_AXI_GP1_ARLOCK,
  output [2:0] M_AXI_GP1_ARSIZE,
  output [1:0] M_AXI_GP1_AWBURST,
  output [1:0] M_AXI_GP1_AWLOCK,
  output [2:0] M_AXI_GP1_AWSIZE,
  output [2:0] M_AXI_GP1_ARPROT,
  output [2:0] M_AXI_GP1_AWPROT,
  output [31:0] M_AXI_GP1_ARADDR,
  output [31:0] M_AXI_GP1_AWADDR,
  output [31:0] M_AXI_GP1_WDATA,
  output [3:0] M_AXI_GP1_ARCACHE,
  output [3:0] M_AXI_GP1_ARLEN,
  output [3:0] M_AXI_GP1_ARQOS,
  output [3:0] M_AXI_GP1_AWCACHE,
  output [3:0] M_AXI_GP1_AWLEN,
  output [3:0] M_AXI_GP1_AWQOS,
  output [3:0] M_AXI_GP1_WSTRB,
  
  // -- Input
  
  input M_AXI_GP1_ACLK,
  input M_AXI_GP1_ARREADY,
  input M_AXI_GP1_AWREADY,
  input M_AXI_GP1_BVALID,
  input M_AXI_GP1_RLAST,
  input M_AXI_GP1_RVALID,
  input M_AXI_GP1_WREADY,  
  input [(C_M_AXI_GP1_THREAD_ID_WIDTH - 1):0] M_AXI_GP1_BID,
  input [(C_M_AXI_GP1_THREAD_ID_WIDTH - 1):0] M_AXI_GP1_RID,
  input [1:0] M_AXI_GP1_BRESP,
  input [1:0] M_AXI_GP1_RRESP,
  input [31:0] M_AXI_GP1_RDATA,  
  

  // S_AXI_GP0
  
  // -- Output
  
  output S_AXI_GP0_ARESETN,
  output S_AXI_GP0_ARREADY,
  output S_AXI_GP0_AWREADY,
  output S_AXI_GP0_BVALID,
  output S_AXI_GP0_RLAST,
  output S_AXI_GP0_RVALID,
  output S_AXI_GP0_WREADY,  
  output [1:0] S_AXI_GP0_BRESP,
  output [1:0] S_AXI_GP0_RRESP,
  output [31:0] S_AXI_GP0_RDATA,
  output [(C_S_AXI_GP0_ID_WIDTH - 1) : 0] S_AXI_GP0_BID,
  output [(C_S_AXI_GP0_ID_WIDTH - 1) : 0] S_AXI_GP0_RID,
  
  // -- Input
  input S_AXI_GP0_ACLK,
  input S_AXI_GP0_ARVALID,
  input S_AXI_GP0_AWVALID,
  input S_AXI_GP0_BREADY,
  input S_AXI_GP0_RREADY,
  input S_AXI_GP0_WLAST,
  input S_AXI_GP0_WVALID,
  input [1:0] S_AXI_GP0_ARBURST,
  input [1:0] S_AXI_GP0_ARLOCK,
  input [2:0] S_AXI_GP0_ARSIZE,
  input [1:0] S_AXI_GP0_AWBURST,
  input [1:0] S_AXI_GP0_AWLOCK,
  input [2:0] S_AXI_GP0_AWSIZE,
  input [2:0] S_AXI_GP0_ARPROT,
  input [2:0] S_AXI_GP0_AWPROT,
  input [31:0] S_AXI_GP0_ARADDR,
  input [31:0] S_AXI_GP0_AWADDR,
  input [31:0] S_AXI_GP0_WDATA,
  input [3:0] S_AXI_GP0_ARCACHE,
  input [3:0] S_AXI_GP0_ARLEN,
  input [3:0] S_AXI_GP0_ARQOS,
  input [3:0] S_AXI_GP0_AWCACHE,
  input [3:0] S_AXI_GP0_AWLEN,
  input [3:0] S_AXI_GP0_AWQOS,
  input [3:0] S_AXI_GP0_WSTRB,
  input [(C_S_AXI_GP0_ID_WIDTH - 1) : 0] S_AXI_GP0_ARID,
  input [(C_S_AXI_GP0_ID_WIDTH - 1) : 0] S_AXI_GP0_AWID,
  input [(C_S_AXI_GP0_ID_WIDTH - 1) : 0] S_AXI_GP0_WID,  

  // S_AXI_GP1
  
  // -- Output  
  output S_AXI_GP1_ARESETN,
  output S_AXI_GP1_ARREADY,
  output S_AXI_GP1_AWREADY,
  output S_AXI_GP1_BVALID,
  output S_AXI_GP1_RLAST,
  output S_AXI_GP1_RVALID,
  output S_AXI_GP1_WREADY,  
  output [1:0] S_AXI_GP1_BRESP,
  output [1:0] S_AXI_GP1_RRESP,
  output [31:0] S_AXI_GP1_RDATA,
  output [(C_S_AXI_GP1_ID_WIDTH - 1) : 0] S_AXI_GP1_BID,
  output [(C_S_AXI_GP1_ID_WIDTH - 1) : 0] S_AXI_GP1_RID,
  
  // -- Input
  input S_AXI_GP1_ACLK,
  input S_AXI_GP1_ARVALID,
  input S_AXI_GP1_AWVALID,
  input S_AXI_GP1_BREADY,
  input S_AXI_GP1_RREADY,
  input S_AXI_GP1_WLAST,
  input S_AXI_GP1_WVALID,
  input [1:0] S_AXI_GP1_ARBURST,
  input [1:0] S_AXI_GP1_ARLOCK,
  input [2:0] S_AXI_GP1_ARSIZE,
  input [1:0] S_AXI_GP1_AWBURST,
  input [1:0] S_AXI_GP1_AWLOCK,
  input [2:0] S_AXI_GP1_AWSIZE,
  input [2:0] S_AXI_GP1_ARPROT,
  input [2:0] S_AXI_GP1_AWPROT,
  input [31:0] S_AXI_GP1_ARADDR,
  input [31:0] S_AXI_GP1_AWADDR,
  input [31:0] S_AXI_GP1_WDATA,
  input [3:0] S_AXI_GP1_ARCACHE,
  input [3:0] S_AXI_GP1_ARLEN,
  input [3:0] S_AXI_GP1_ARQOS,
  input [3:0] S_AXI_GP1_AWCACHE,
  input [3:0] S_AXI_GP1_AWLEN,
  input [3:0] S_AXI_GP1_AWQOS,
  input [3:0] S_AXI_GP1_WSTRB,
  input [(C_S_AXI_GP1_ID_WIDTH - 1) : 0] S_AXI_GP1_ARID,
  input [(C_S_AXI_GP1_ID_WIDTH - 1) : 0] S_AXI_GP1_AWID,
  input [(C_S_AXI_GP1_ID_WIDTH - 1) : 0] S_AXI_GP1_WID,
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
