fpga-theremin/theremin/fpga/ip_repo/theremin_ip/src/theremin_i2c/tb/theremin_i2c_tb.sv

`timescale 1ns / 1ps
//////////////////////////////////////////////////////////////////////////////////
// Company: 
// Engineer: 
// 
// Create Date: 09/25/2018 01:11:14 PM
// Design Name: 
// Module Name: theremin_audio_i2c_tb
// Project Name: 
// Target Devices: 
// Tool Versions: 
// Description: 
// 
// Dependencies: 
// 
// Revision:
// Revision 0.01 - File Created
// Additional Comments:
// 
//////////////////////////////////////////////////////////////////////////////////


//`define debug_theremin_audio_i2c

module theremin_i2c_tb(

    );

reg CLK;
reg RESET;

reg [23:0] COMMAND;  // [23:16] - device address/op, [15:8] register address, [7:0] data to write
reg START;           // 1 for one CLK_100 cycle to start operation according to COMMAND
wire [7:0] DATA_OUT; // data read from I2C
wire READY;
wire ERROR;

wire I2C_DATA;
wire I2C_CLK;        // 400KHz

`ifdef debug_theremin_audio_i2c
    wire [4:0] debug_state_reg;
    wire debug_phase0;
    wire debug_phase1;
    wire debug_phase2;
    wire debug_phase3;
    wire debug_buf_tri;
    wire debug_i2c_data_reg;
    wire [7:0] debug_out_shift_reg;
    wire [7:0] debug_input_shift_reg;
    wire [23:0] debug_command_reg;
`endif


theremin_i2c theremin_i2c_inst (
    .*
);

`define assert(signal, value) \
        if (signal !== value) begin \
            $display("ASSERTION FAILED in %m: signal != value (%h != %h)   dec (%d != %d)", signal, value, signal, value); \
            $finish; \
        end
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
